griffinross2/Topiary-TrimBot/software/images/left_0.jpg

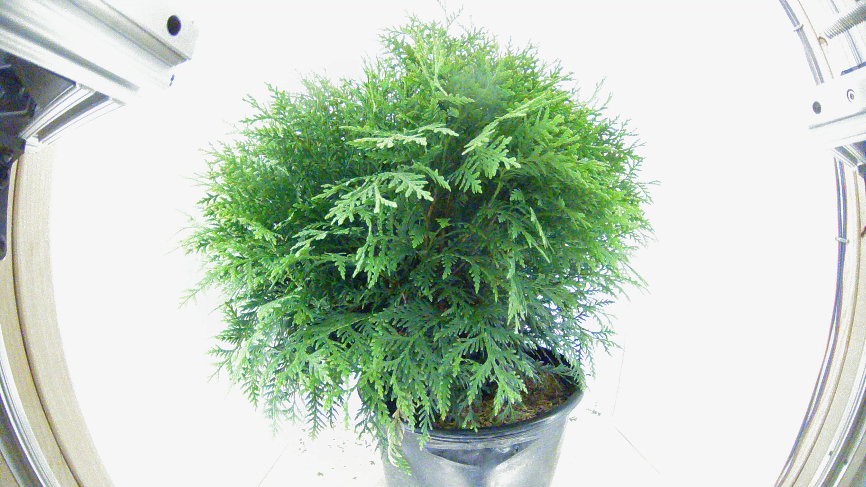
software/images/left_0.jpg
