griffinross2/Topiary-TrimBot/software/images/left_30.jpg

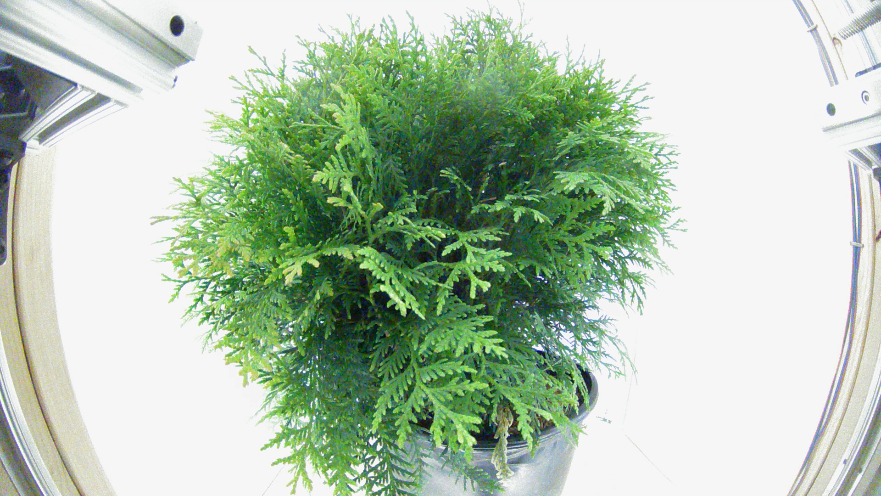
software/images/left_30.jpg
