griffinross2/Topiary-TrimBot/software/images/left_60.jpg

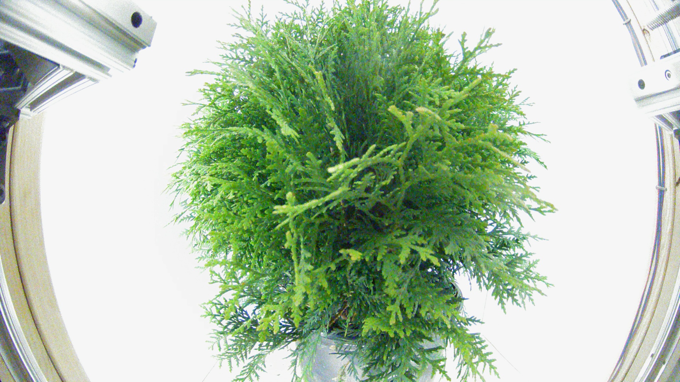
software/images/left_60.jpg
