griffinross2/Topiary-TrimBot/software/images/left_90.jpg

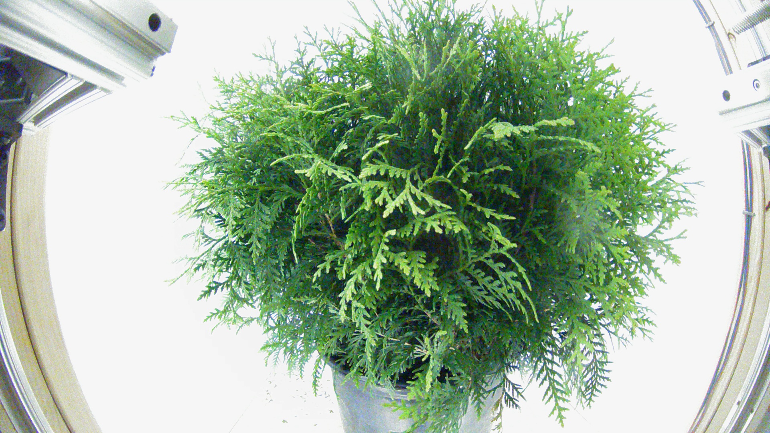
software/images/left_90.jpg
