griffinross2/Topiary-TrimBot/software/images/left_120.jpg

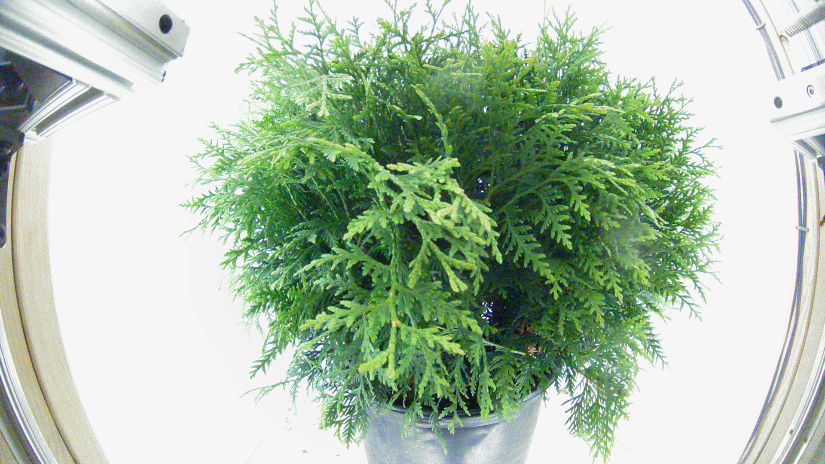
software/images/left_120.jpg
