griffinross2/Topiary-TrimBot/software/images/left_150.jpg

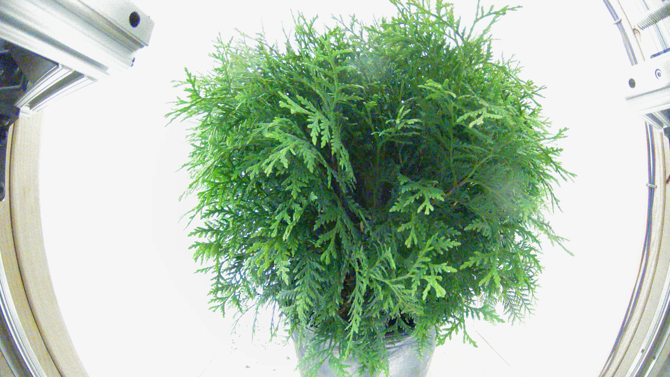
software/images/left_150.jpg
