griffinross2/Topiary-TrimBot/software/images/left_210.jpg

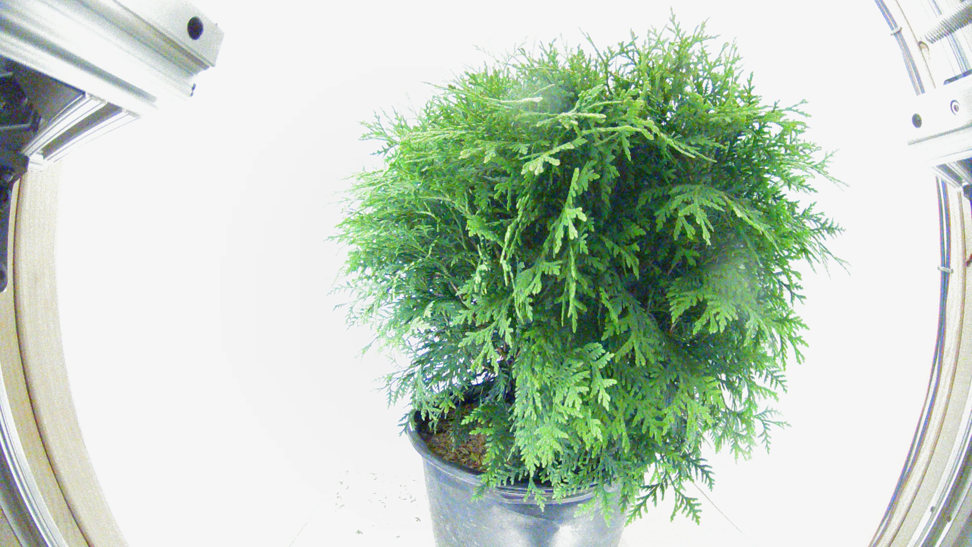
software/images/left_210.jpg
