griffinross2/Topiary-TrimBot/software/images/left_240.jpg

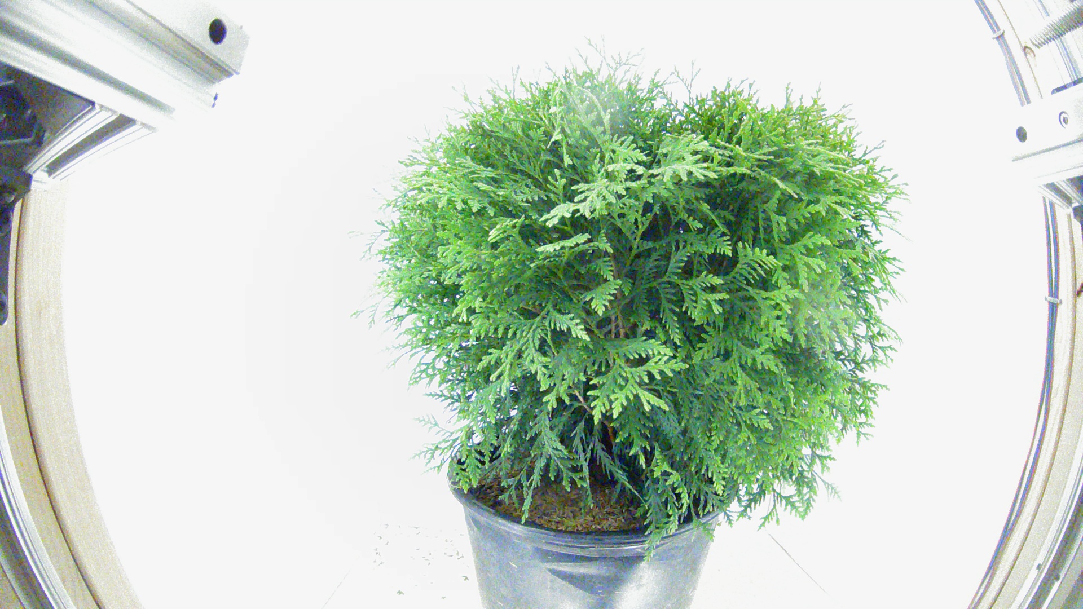
software/images/left_240.jpg
