griffinross2/Topiary-TrimBot/software/images/left_270.jpg

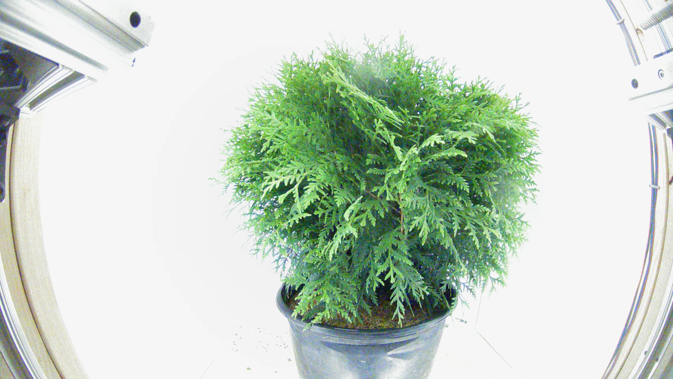
software/images/left_270.jpg
