griffinross2/Topiary-TrimBot/software/images/left_330.jpg

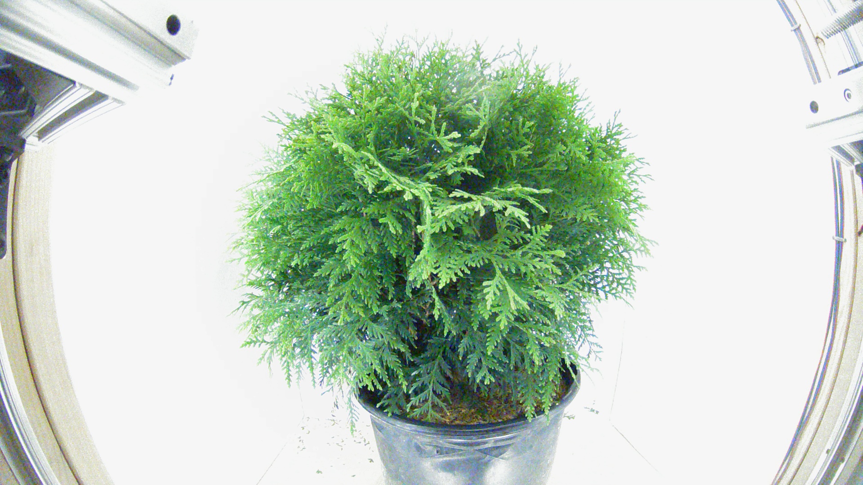
software/images/left_330.jpg
