griffinross2/Topiary-TrimBot/software/images/right_0.jpg

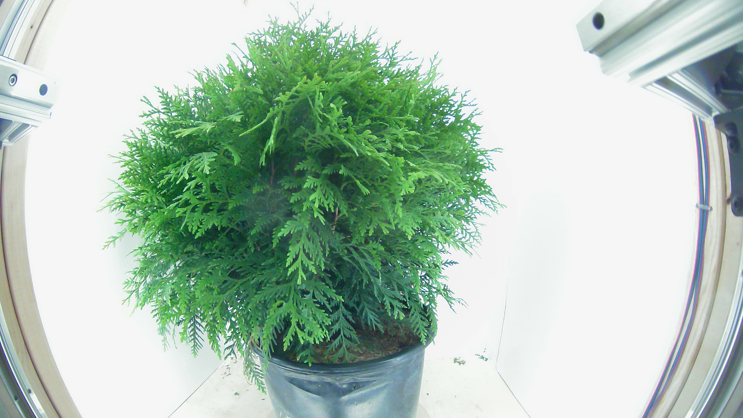
software/images/right_0.jpg
