griffinross2/Topiary-TrimBot/software/images/right_30.jpg

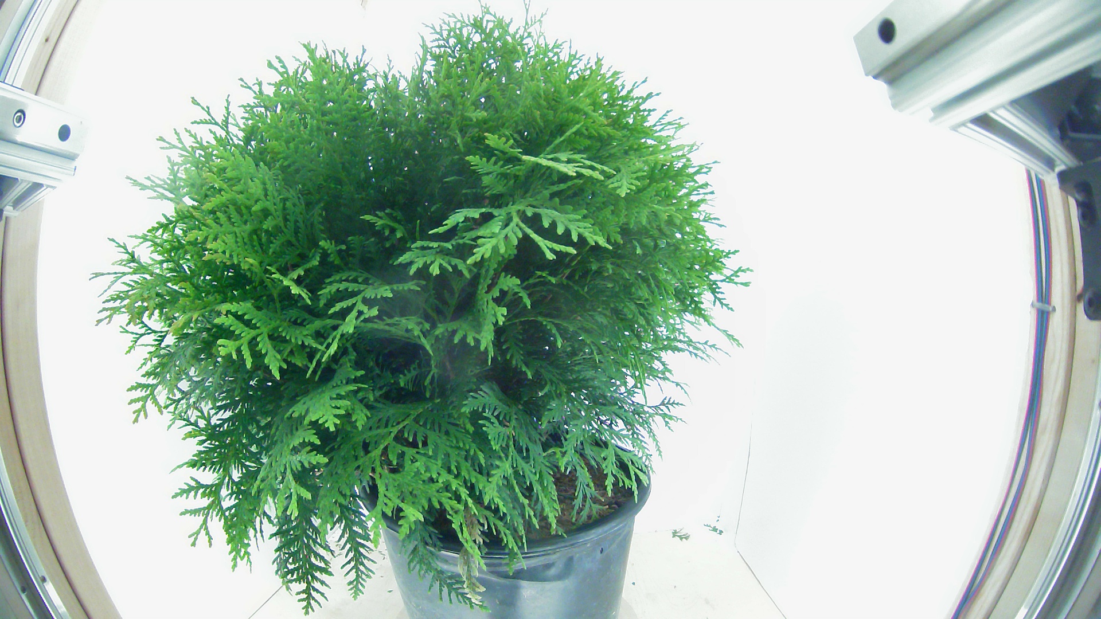
software/images/right_30.jpg
