griffinross2/Topiary-TrimBot/software/images/right_60.jpg

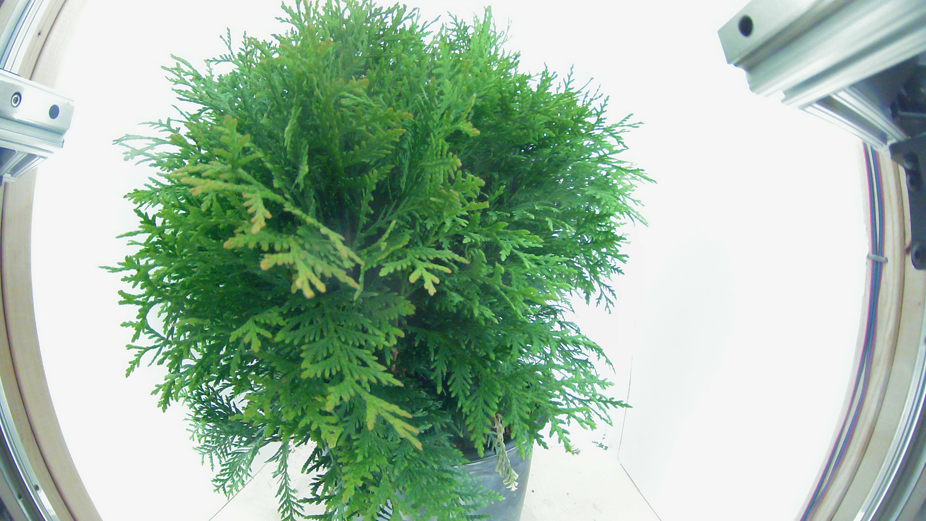
software/images/right_60.jpg
