griffinross2/Topiary-TrimBot/software/images/right_90.jpg

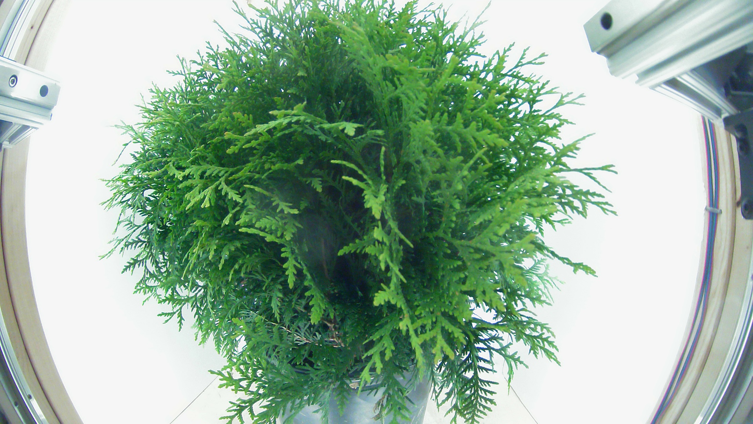
software/images/right_90.jpg
