griffinross2/Topiary-TrimBot/software/images/right_120.jpg

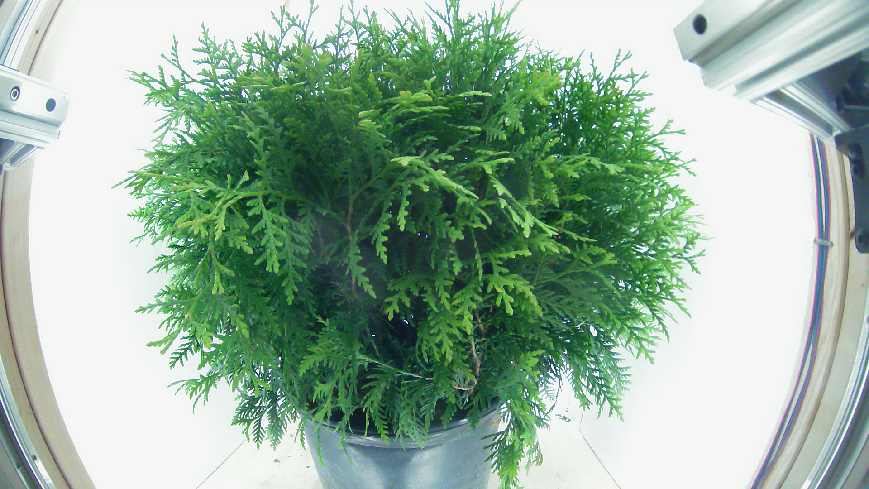
software/images/right_120.jpg
