griffinross2/Topiary-TrimBot/software/images/right_180.jpg

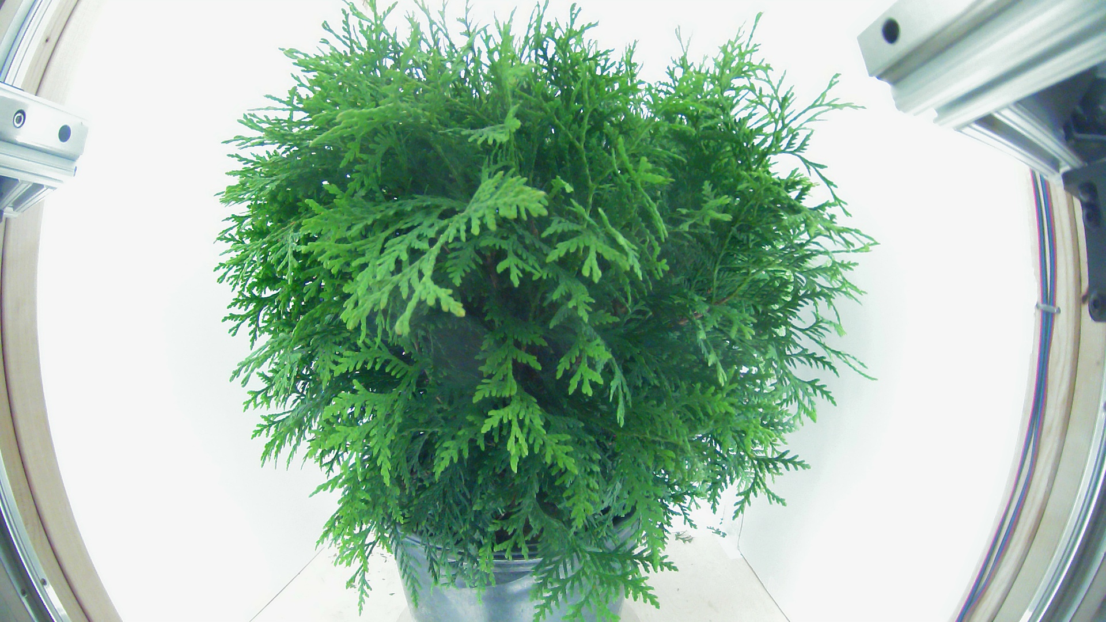
software/images/right_180.jpg
