griffinross2/Topiary-TrimBot/software/images/right_270.jpg

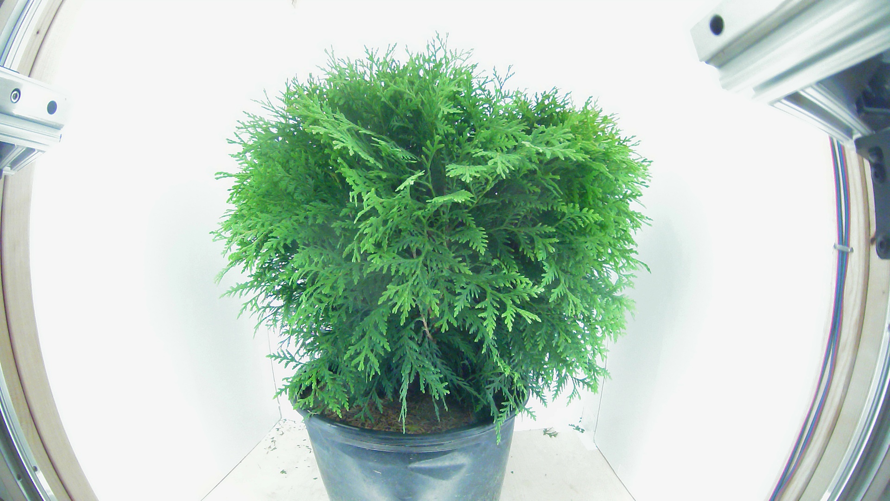
software/images/right_270.jpg
