griffinross2/Topiary-TrimBot/software/images/right_330.jpg

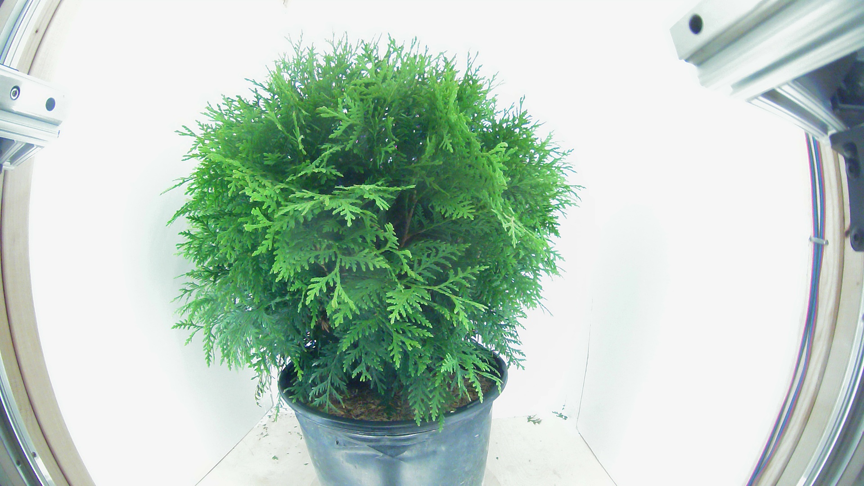
software/images/right_330.jpg
