griffinross2/Topiary-TrimBot/software/vision/checkerboards/WIN_20260413_22_22_19_Pro.jpg

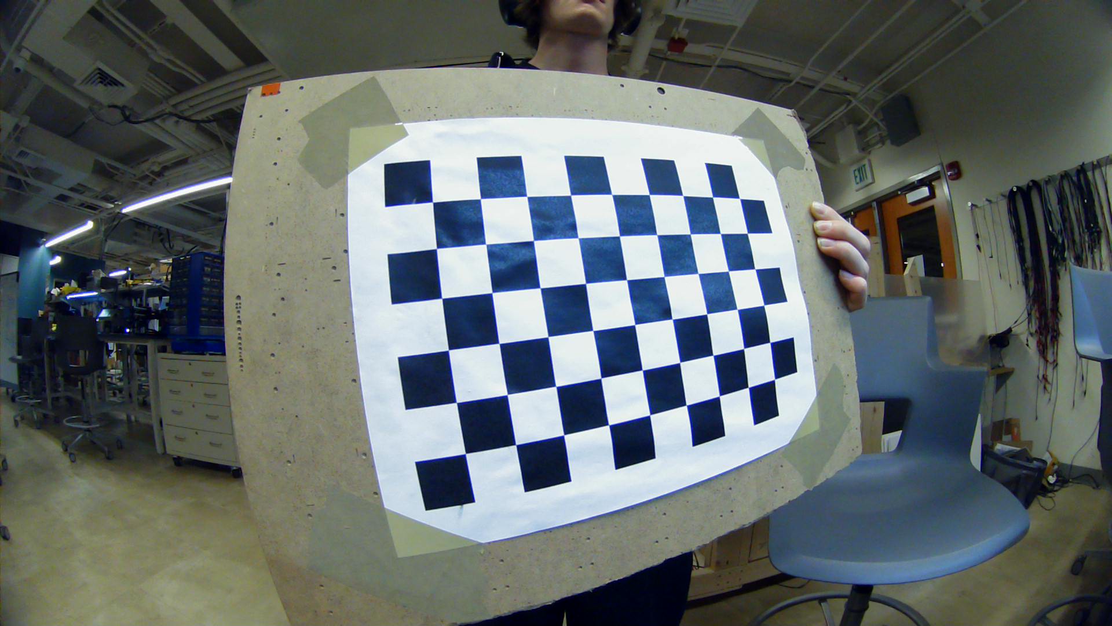
software/vision/checkerboards/WIN_20260413_22_22_19_Pro.jpg
