griffinross2/Topiary-TrimBot/software/vision/checkerboards/WIN_20260413_22_38_03_Pro.jpg

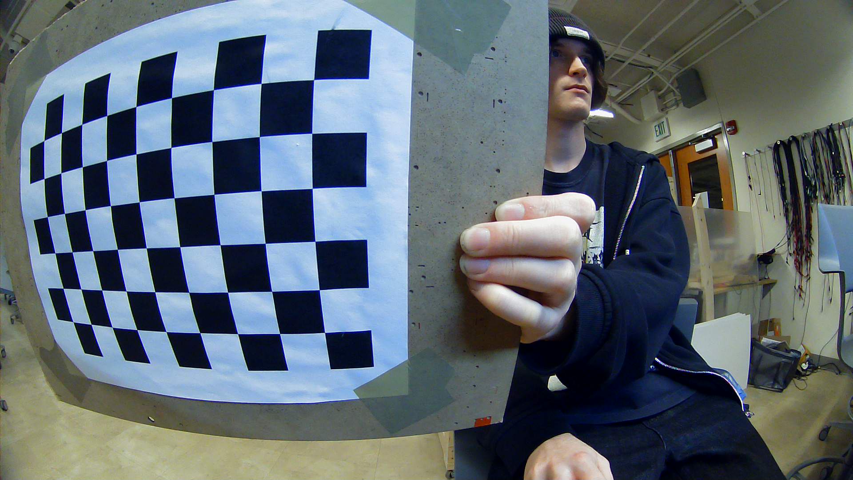
software/vision/checkerboards/WIN_20260413_22_38_03_Pro.jpg
