griffinross2/Topiary-TrimBot/software/vision/checkerboards/WIN_20260414_17_03_58_Pro.jpg

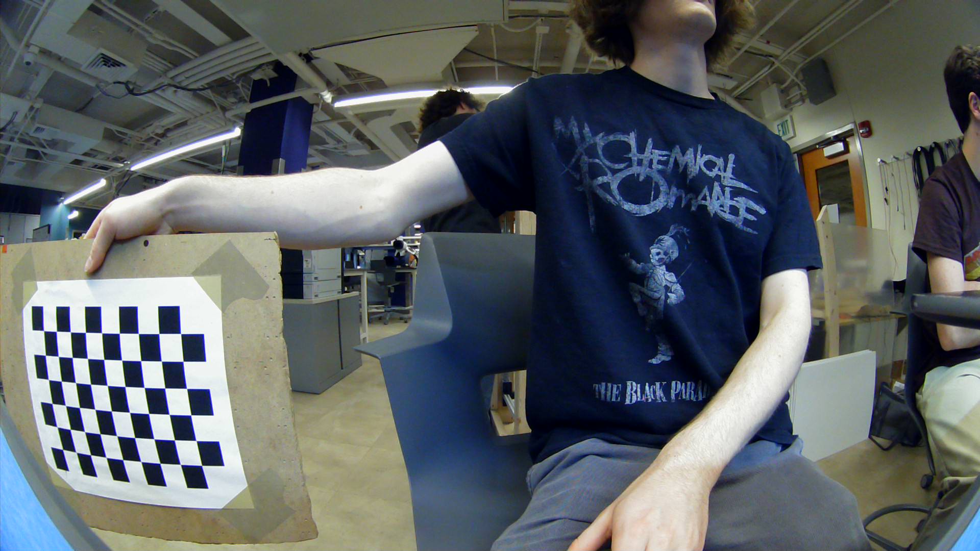
software/vision/checkerboards/WIN_20260414_17_03_58_Pro.jpg
