griffinross2/Topiary-TrimBot/experimental/cpp/plant_detect/images/pi/cal_5.jpg

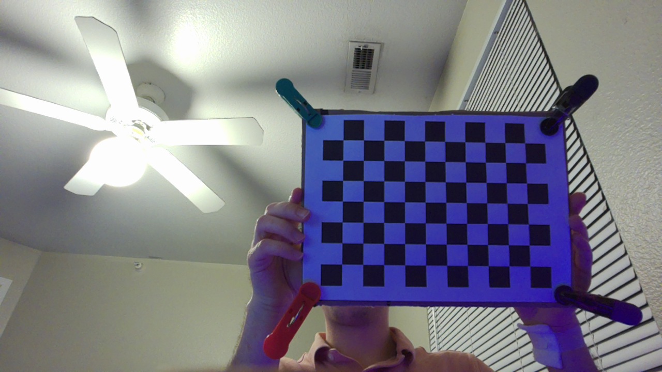
experimental/cpp/plant_detect/images/pi/cal_5.jpg
