griffinross2/Topiary-TrimBot/experimental/cpp/plant_detect/images/pi/cal_6.jpg

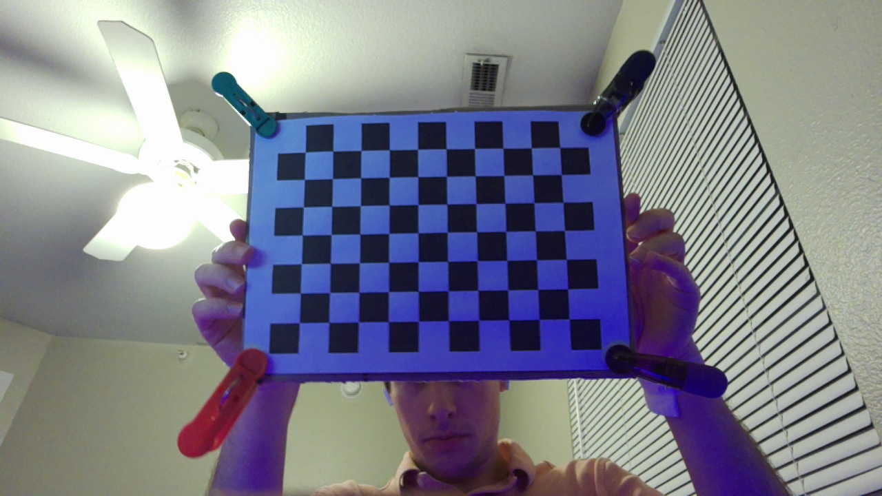
experimental/cpp/plant_detect/images/pi/cal_6.jpg
