griffinross2/Topiary-TrimBot/experimental/cpp/plant_detect/images/WIN_20251111_21_14_15_Pro.jpg

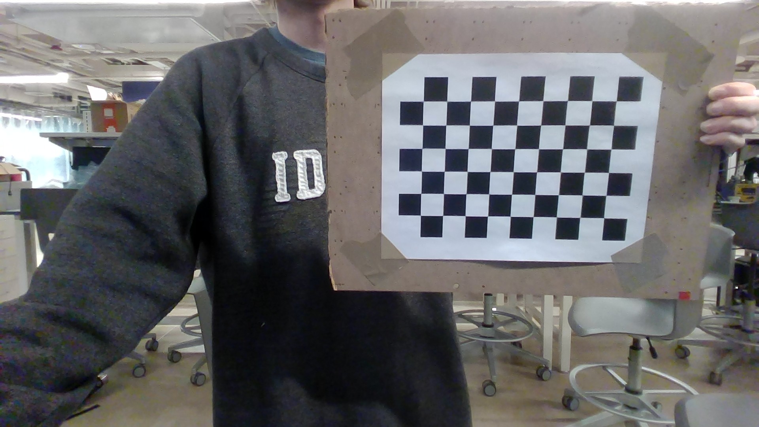
experimental/cpp/plant_detect/images/WIN_20251111_21_14_15_Pro.jpg
