griffinross2/Topiary-TrimBot/experimental/cpp/plant_detect/images/WIN_20251111_21_15_57_Pro.jpg

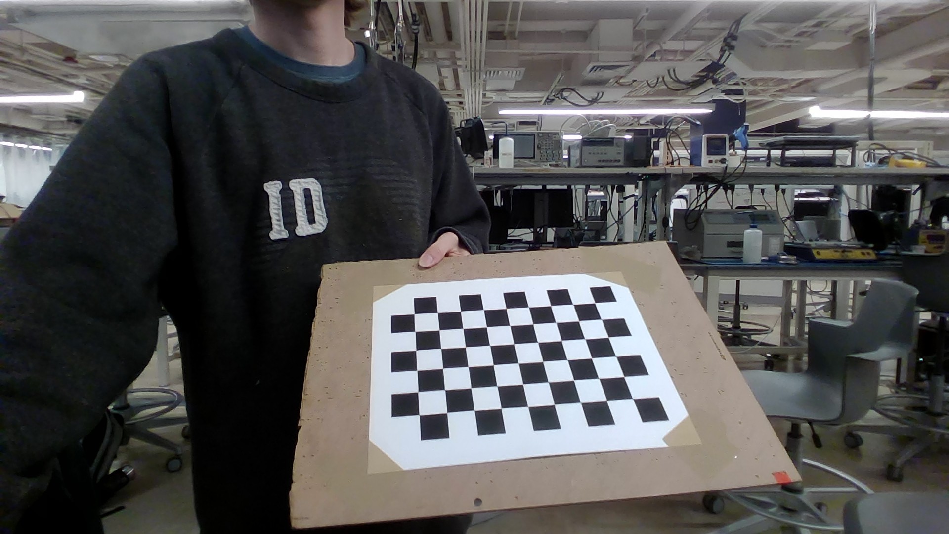
experimental/cpp/plant_detect/images/WIN_20251111_21_15_57_Pro.jpg
