griffinross2/Topiary-TrimBot/experimental/python-notebooks/plant_detect/image324x324outside.jpg

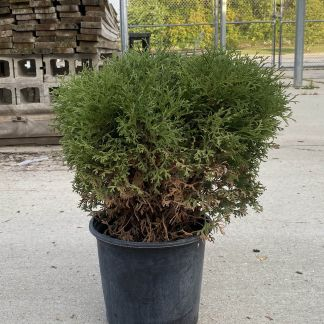
experimental/python-notebooks/plant_detect/image324x324outside.jpg
