griffinross2/Topiary-TrimBot/experimental/python-notebooks/plant_detect/left_rot_1.jpg

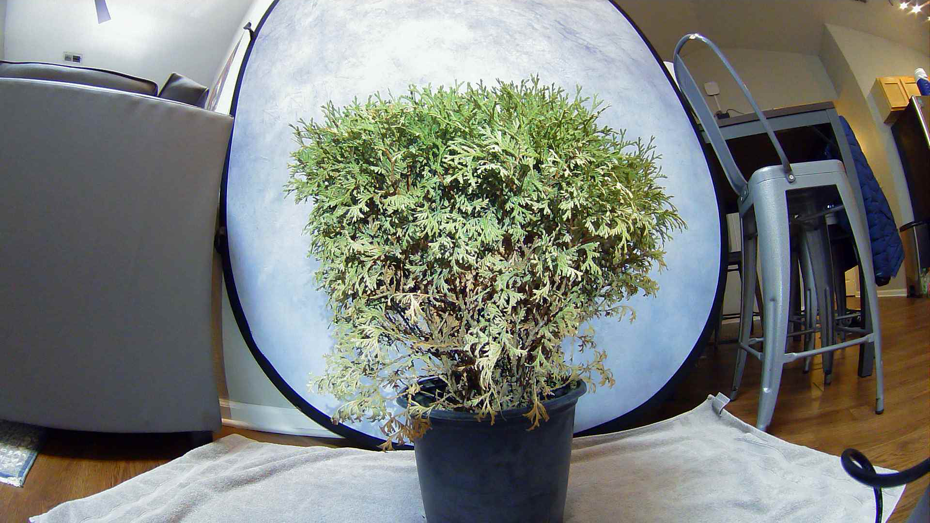
experimental/python-notebooks/plant_detect/left_rot_1.jpg
