griffinross2/Topiary-TrimBot/software/calibration_images/left/0.jpg

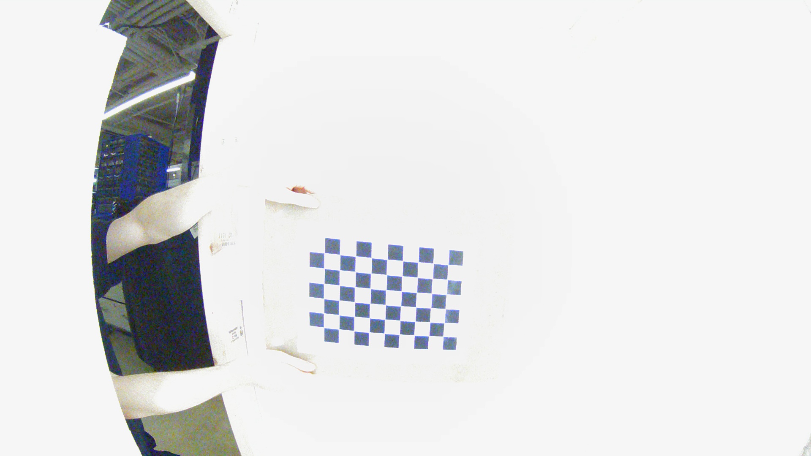
software/calibration_images/left/0.jpg
