griffinross2/Topiary-TrimBot/software/calibration_images/left/1.jpg

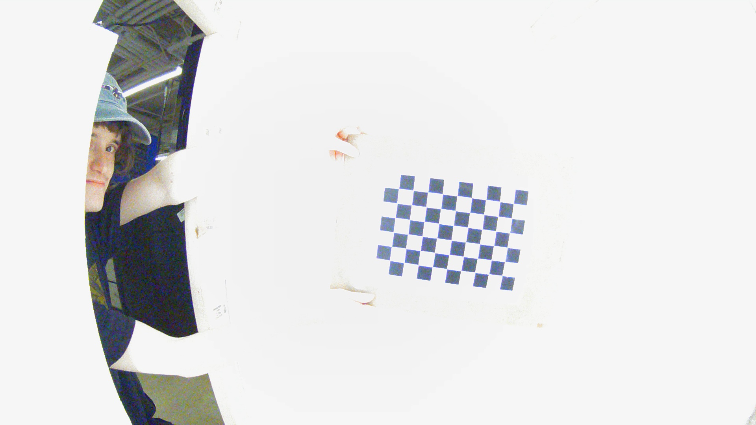
software/calibration_images/left/1.jpg
