griffinross2/Topiary-TrimBot/software/calibration_images/left/2.jpg

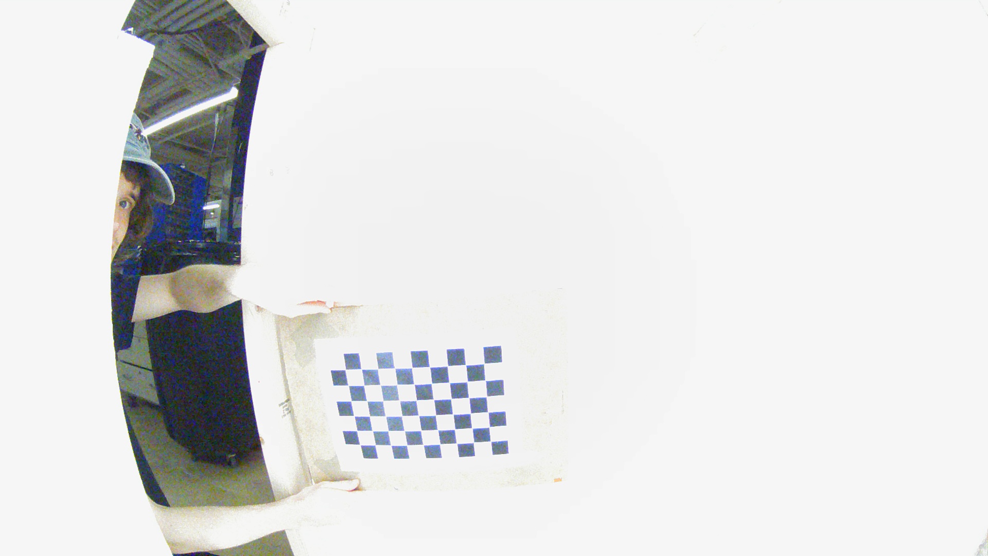
software/calibration_images/left/2.jpg
