griffinross2/Topiary-TrimBot/software/calibration_images/left/3.jpg

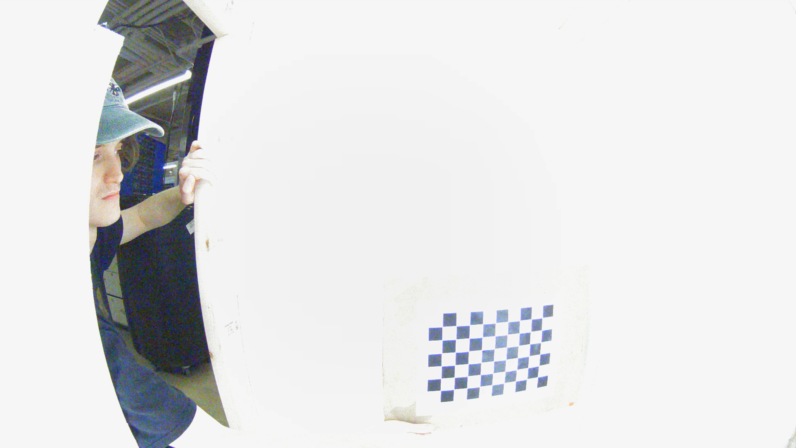
software/calibration_images/left/3.jpg
