griffinross2/Topiary-TrimBot/software/calibration_images/left/5.jpg

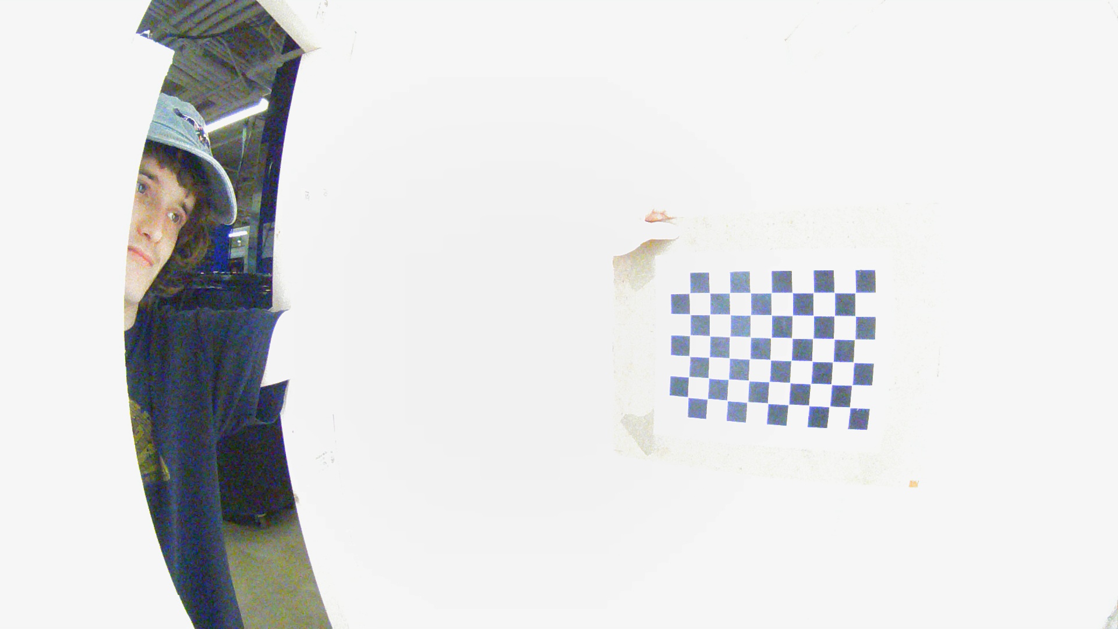
software/calibration_images/left/5.jpg
