griffinross2/Topiary-TrimBot/software/calibration_images/left/6.jpg

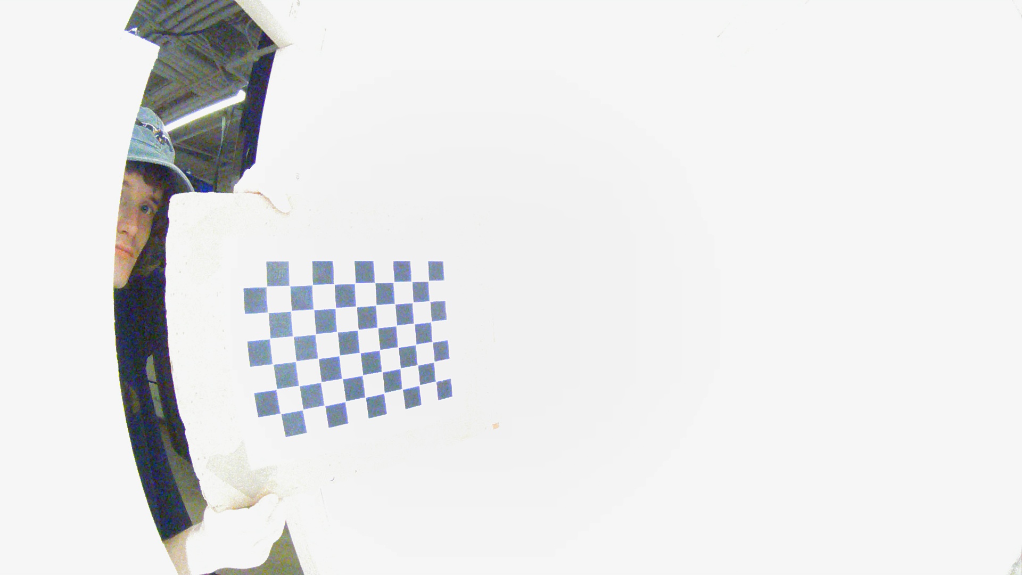
software/calibration_images/left/6.jpg
