griffinross2/Topiary-TrimBot/software/calibration_images/left/8.jpg

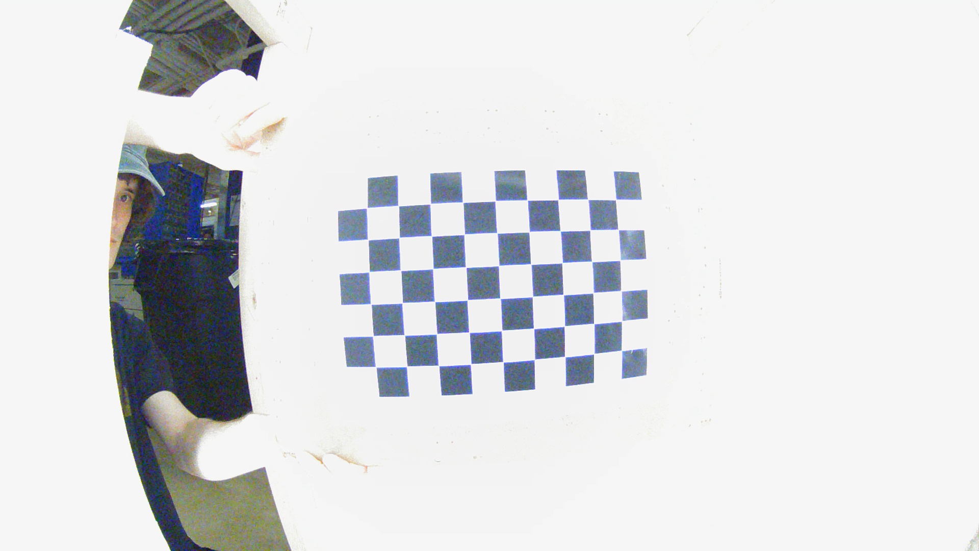
software/calibration_images/left/8.jpg
