griffinross2/Topiary-TrimBot/software/calibration_images/left/10.jpg

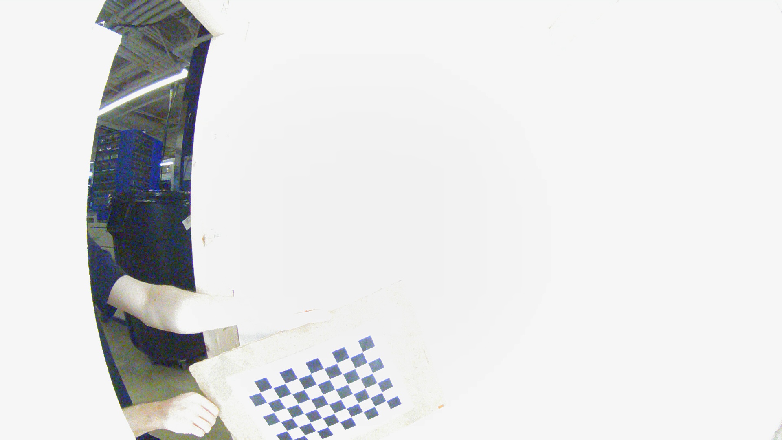
software/calibration_images/left/10.jpg
