griffinross2/Topiary-TrimBot/software/calibration_images/left/13.jpg

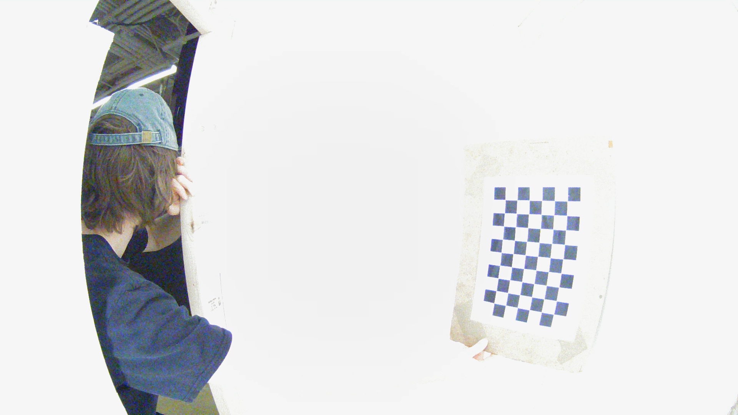
software/calibration_images/left/13.jpg
