griffinross2/Topiary-TrimBot/software/calibration_images/left/14.jpg

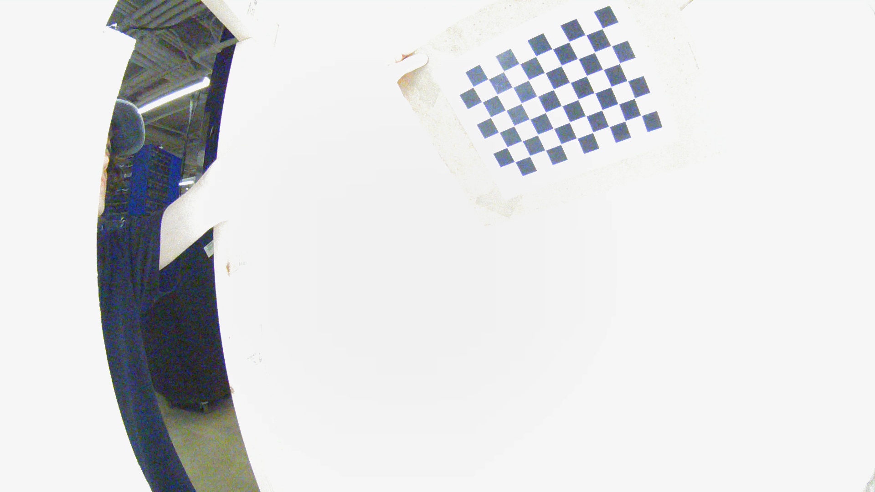
software/calibration_images/left/14.jpg
