griffinross2/Topiary-TrimBot/software/calibration_images/left/15.jpg

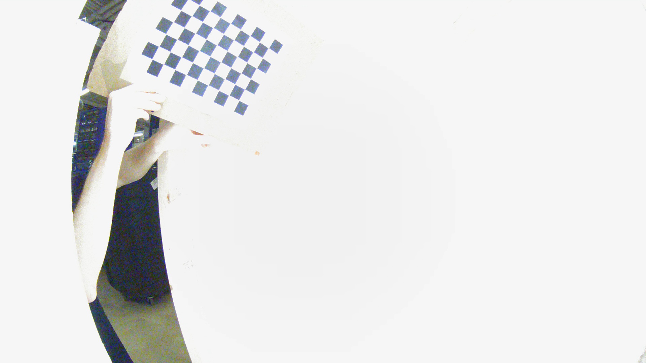
software/calibration_images/left/15.jpg
