griffinross2/Topiary-TrimBot/software/calibration_images/left/16.jpg

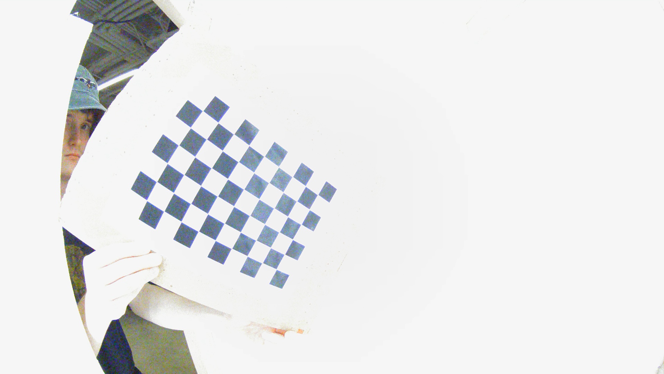
software/calibration_images/left/16.jpg
