griffinross2/Topiary-TrimBot/software/calibration_images/left/18.jpg

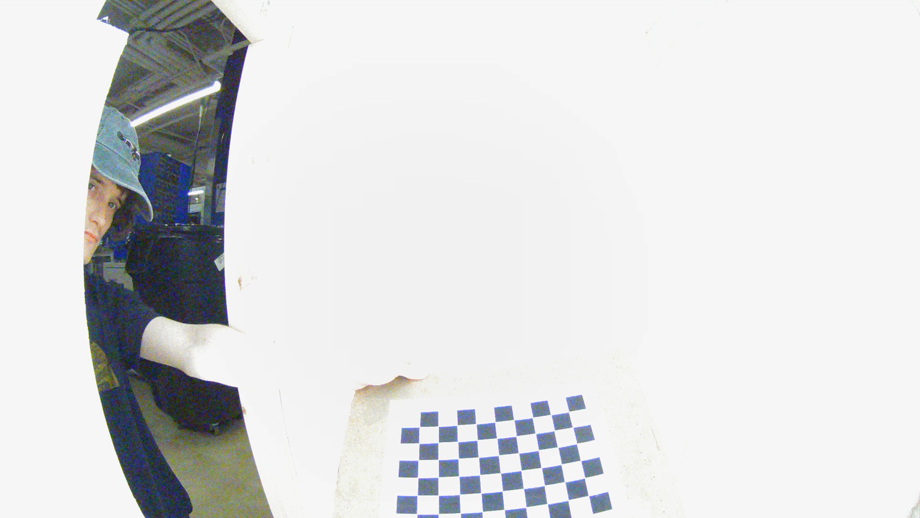
software/calibration_images/left/18.jpg
