griffinross2/Topiary-TrimBot/software/calibration_images/left/19.jpg

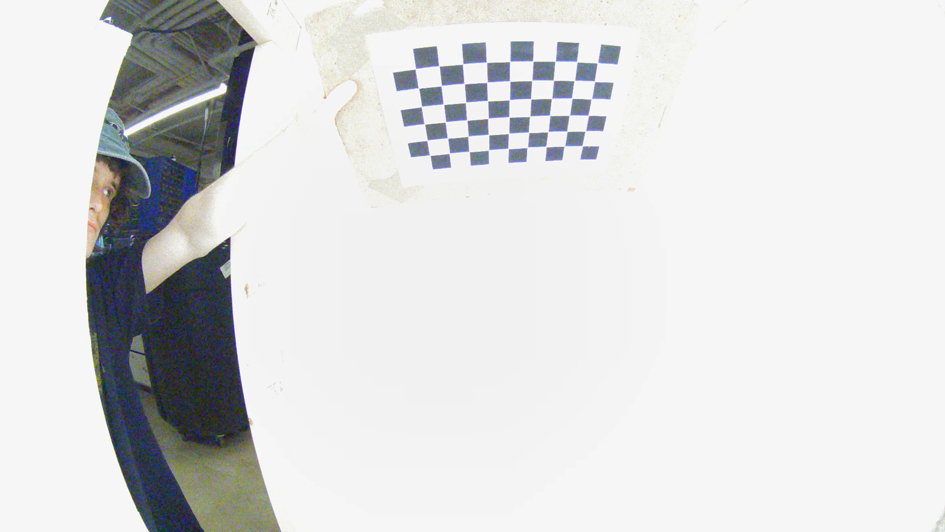
software/calibration_images/left/19.jpg
