griffinross2/Topiary-TrimBot/software/calibration_images/right/1.jpg

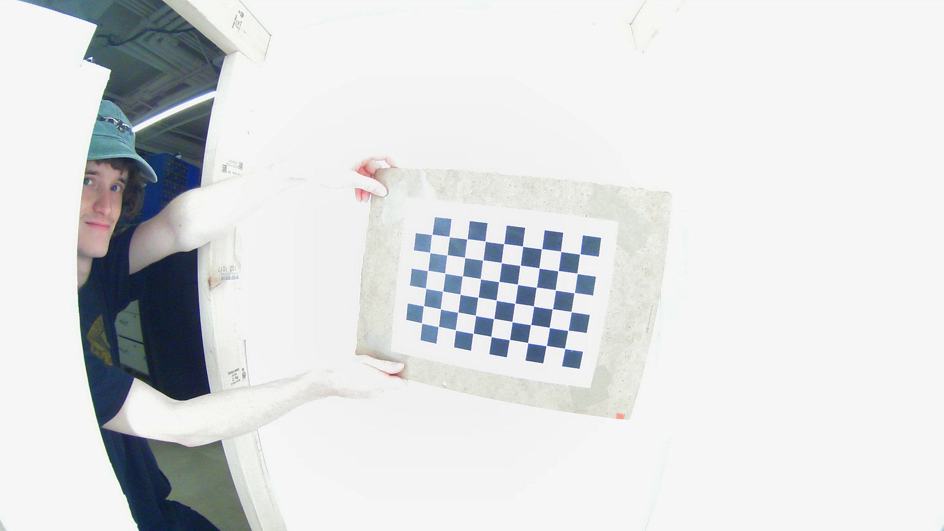
software/calibration_images/right/1.jpg
