griffinross2/Topiary-TrimBot/software/calibration_images/right/2.jpg

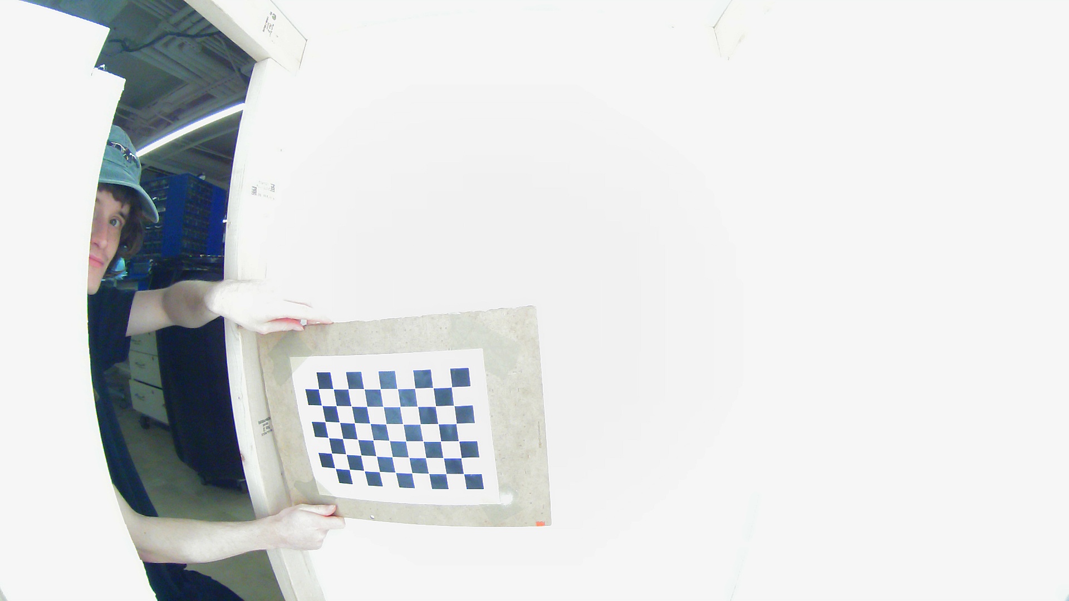
software/calibration_images/right/2.jpg
