griffinross2/Topiary-TrimBot/software/calibration_images/right/3.jpg

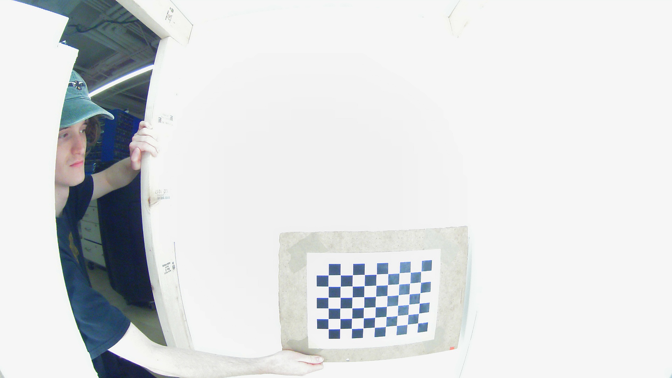
software/calibration_images/right/3.jpg
