griffinross2/Topiary-TrimBot/software/calibration_images/right/5.jpg

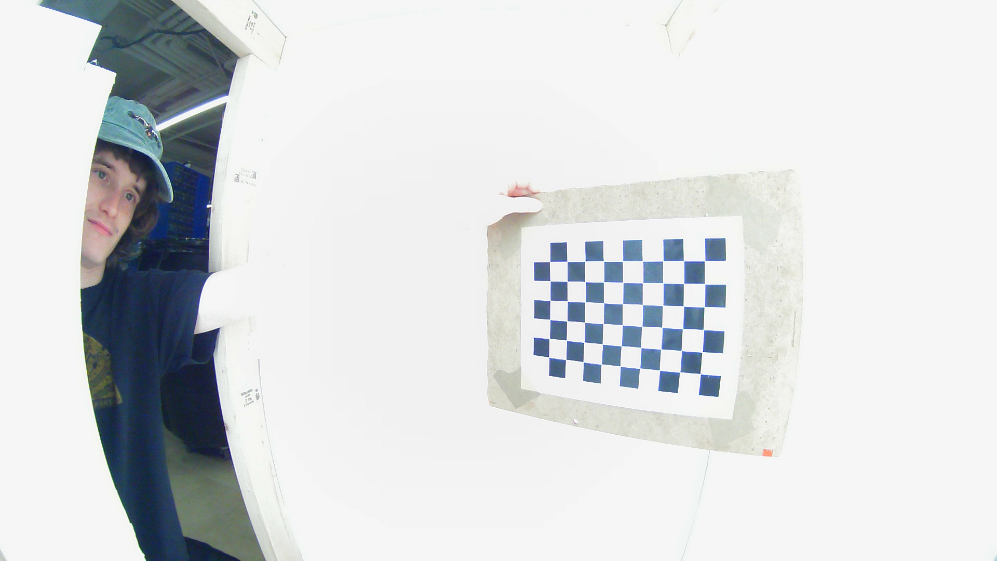
software/calibration_images/right/5.jpg
