griffinross2/Topiary-TrimBot/software/calibration_images/right/6.jpg

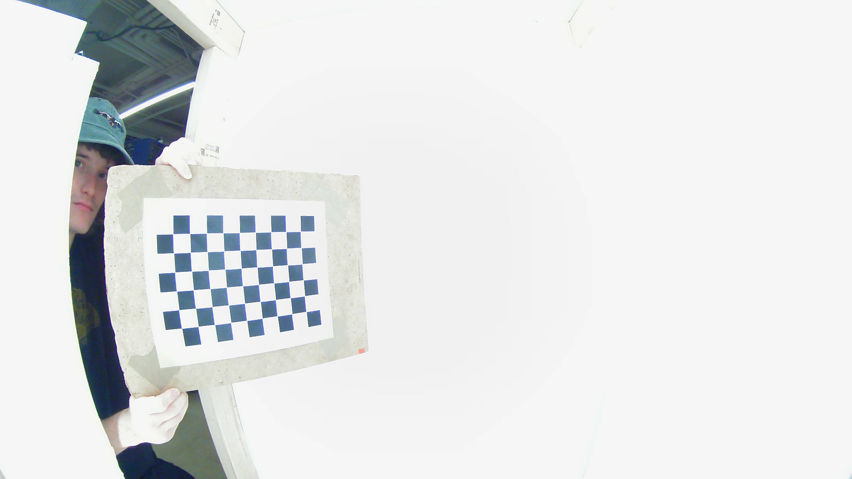
software/calibration_images/right/6.jpg
