griffinross2/Topiary-TrimBot/software/calibration_images/right/7.jpg

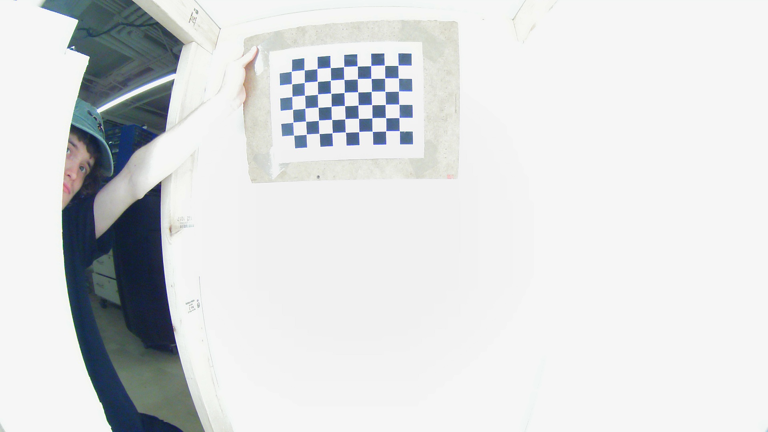
software/calibration_images/right/7.jpg
