griffinross2/Topiary-TrimBot/software/calibration_images/right/10.jpg

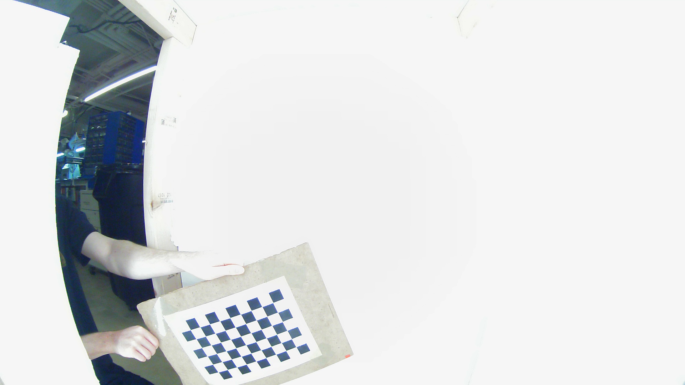
software/calibration_images/right/10.jpg
