griffinross2/Topiary-TrimBot/software/calibration_images/right/11.jpg

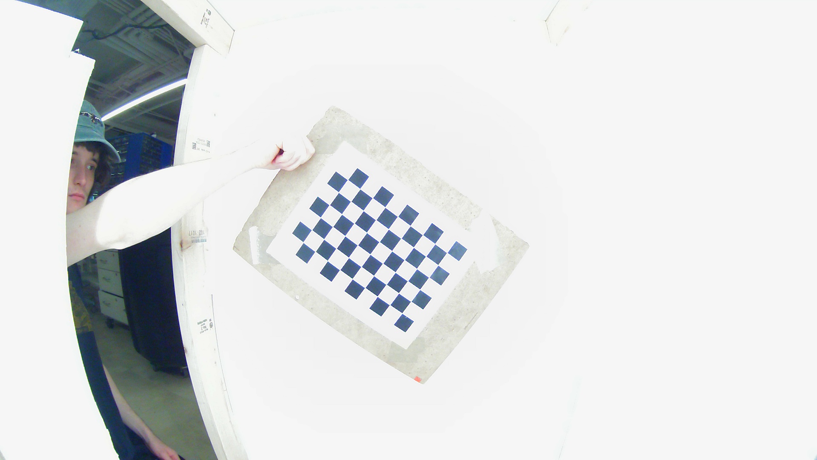
software/calibration_images/right/11.jpg
