griffinross2/Topiary-TrimBot/software/calibration_images/right/13.jpg

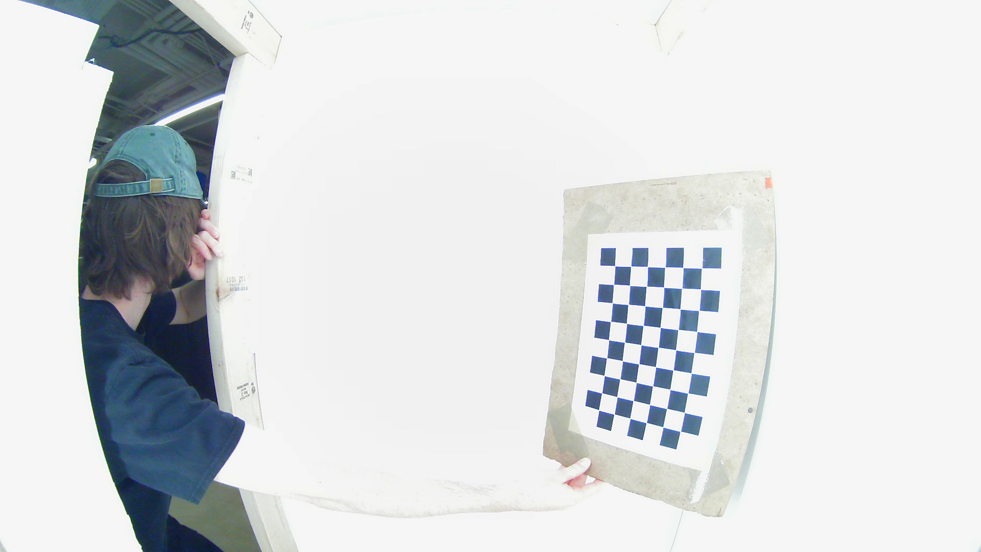
software/calibration_images/right/13.jpg
