griffinross2/Topiary-TrimBot/software/calibration_images/right/14.jpg

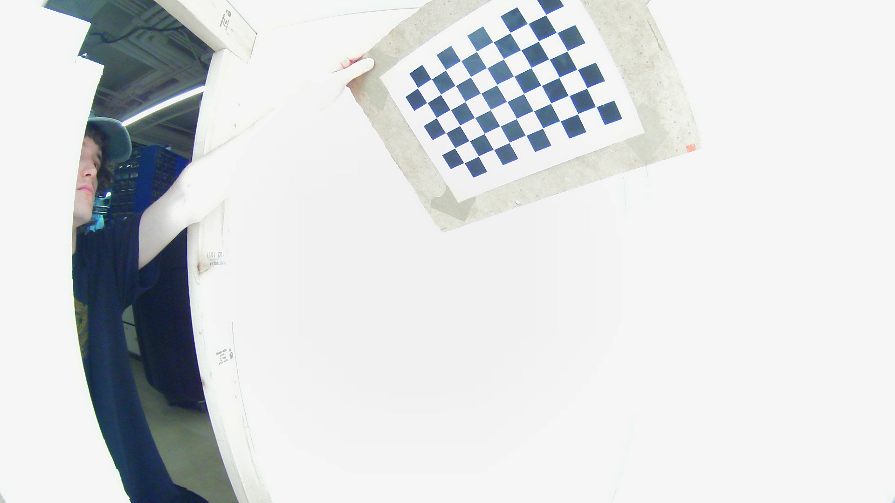
software/calibration_images/right/14.jpg
