griffinross2/Topiary-TrimBot/software/calibration_images/right/15.jpg

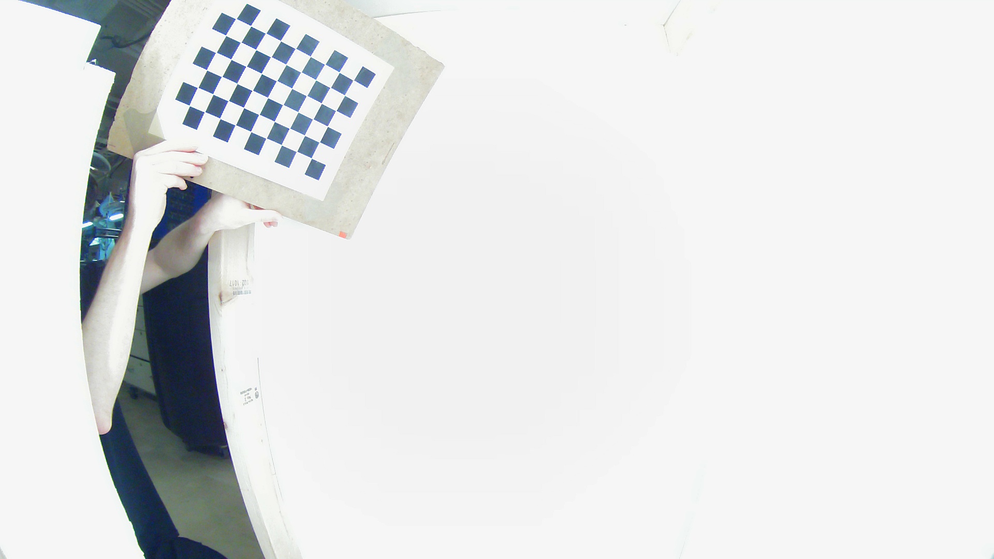
software/calibration_images/right/15.jpg
