griffinross2/Topiary-TrimBot/software/calibration_images/right/16.jpg

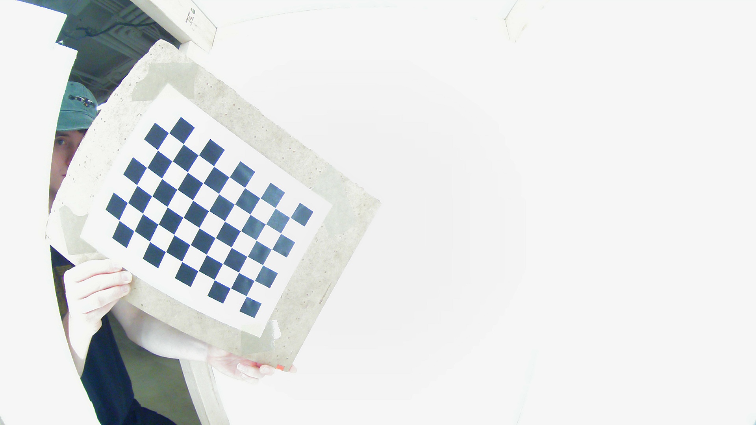
software/calibration_images/right/16.jpg
