griffinross2/Topiary-TrimBot/software/calibration_images/right/17.jpg

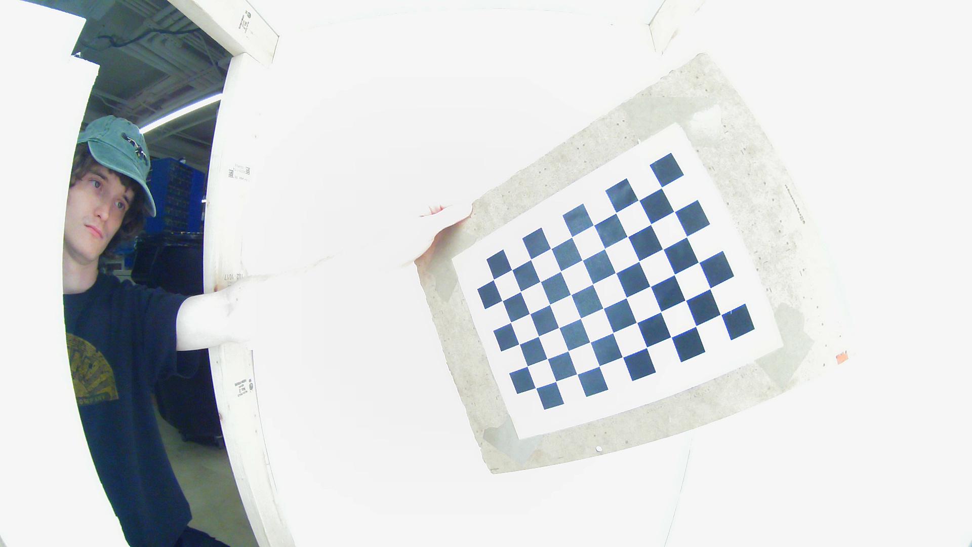
software/calibration_images/right/17.jpg
