griffinross2/Topiary-TrimBot/software/calibration_images/right/18.jpg

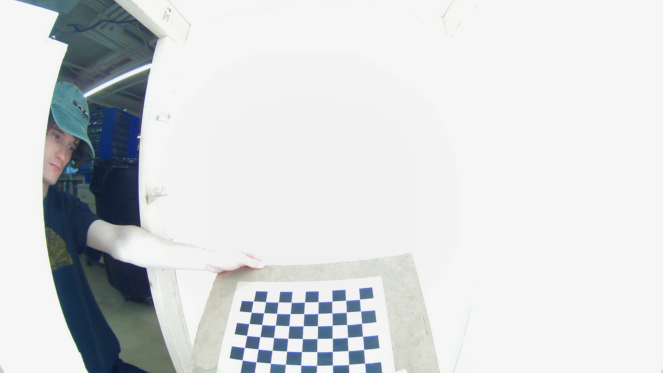
software/calibration_images/right/18.jpg
