griffinross2/Topiary-TrimBot/software/crc16.py

# crc16.py based on:
# Github Gist by rafacouto : https://gist.github.com/rafacouto/59326c90d6a55f86a3ba

ccitt_hash = [
    0x0000,
    0x1021,
    0x2042,
    0x3063,
    0x4084,
    0x50a5,
    0x60c6,
    0x70e7,
    0x8108,
    0x9129,
    0xa14a,
    0xb16b,
    0xc18c,
    0xd1ad,
    0xe1ce,
    0xf1ef,
    0x1231,
    0x0210,
    0x3273,
    0x2252,
    0x52b5,
    0x4294,
    0x72f7,
    0x62d6,
    0x9339,
    0x8318,
    0xb37b,
    0xa35a,
    0xd3bd,
    0xc39c,
    0xf3ff,
    0xe3de,
    0x2462,
    0x3443,
    0x0420,
    0x1401,
    0x64e6,
    0x74c7,
    0x44a4,
    0x5485,
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
]

def crc16_ccitt(buffer: bytes):
    idx = 0
    size = len(buffer)

    crc = 0
    while size > 0:
        size -= 1
        crc = (crc << 8) ^ ccitt_hash[((crc >> 8) ^ buffer[idx]) & 0x00FF]
        idx += 1

    return crc & 0xFFFF
