griffinross2/Topiary-TrimBot/experimental/lcd_prototyping/Core/Src/main.c

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
/* Includes ------------------------------------------------------------------*/
#include "main.h"

/* USER CODE BEGIN Includes */
#include <stdio.h>
#include "lcd.h"
/* USER CODE END Includes */

DSI_HandleTypeDef hdsi;

I2C_HandleTypeDef hi2c1;

LTDC_HandleTypeDef hltdc;

TIM_HandleTypeDef htim3;

UART_HandleTypeDef huart6;

SDRAM_HandleTypeDef hsdram1;

void SystemClock_Config(void);
static void MX_GPIO_Init(void);
static void MX_USART6_UART_Init(void);
static void MX_LTDC_Init(void);
static void MX_DSIHOST_DSI_Init(void);
static void MX_FMC_Init(void);
static void MX_I2C1_Init(void);
static void MX_TIM3_Init(void);
/* USER CODE BEGIN 0 */
int __io_putchar(int ch) {
	HAL_UART_Transmit(&huart6, (uint8_t*)&ch, 1, 50);
	return ch;
}
/* USER CODE END 0 */

/**
  * @brief  The application entry point.
  * @retval int
  */
int main(void)
{

  /* MCU Configuration--------------------------------------------------------*/

  /* Reset of all peripherals, Initializes the Flash interface and the Systick. */
  HAL_Init();

  /* Configure the system clock */
  SystemClock_Config();

  /* Initialize all configured peripherals */
  MX_GPIO_Init();
  MX_USART6_UART_Init();
  MX_LTDC_Init();
  MX_DSIHOST_DSI_Init();
  MX_FMC_Init();
  MX_I2C1_Init();
  MX_TIM3_Init();
  /* USER CODE BEGIN 2 */
  if (lcd_init() != LCD_OK) {
	  printf("LCD failed to initialize!\n");
	  return 1;
  }
  printf("LCD init success\n");
  /* USER CODE END 2 */

  /* Infinite loop */
  /* USER CODE BEGIN WHILE */
  while (1)
  {
    /* USER CODE END WHILE */

    /* USER CODE BEGIN 3 */
	  printf("cuh\n");
	  HAL_Delay(1000);
  }

  return 0;
  /* USER CODE END 3 */
}

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
