griffinross2/Topiary-TrimBot/experimental/lcd_prototyping_platformio/src/lcd.cpp

/*
 * lcd.c
 *
 *  Created on: Nov 11, 2025
 *      Author: griff
 */

#include "lcd.h"

#include <stdio.h>
#include <string.h>
#include <algorithm>

#include "ltdc_dsi.h"
#include "nt35510.h"
#include "ft6336g.h"
#include "profiler.h"

#define LCD_RESET_PORT GPIOH
#define LCD_RESET_PIN GPIO_PIN_7

DSI_HandleTypeDef* hdsi;
LTDC_HandleTypeDef* hltdc;
DMA2D_HandleTypeDef hdma2d;

// Double-buffered setup
static ColorRGB565 __attribute__((
    section(".ext_ram"))) s_foreground_buffer_0[LCD_WIDTH * LCD_HEIGHT];
static ColorRGB565 __attribute__((
    section(".ext_ram"))) s_foreground_buffer_1[LCD_WIDTH * LCD_HEIGHT];

static ColorRGB565** s_foreground_buffers = (ColorRGB565*[]){
    s_foreground_buffer_0,
    s_foreground_buffer_1,
};
static volatile int s_current_frontbuffer = 0;

// Sorry about macros
#define FRONTBUFFER s_foreground_buffers[s_current_frontbuffer]
#define BACKBUFFER s_foreground_buffers[1 - s_current_frontbuffer]

// EOF callback
void lcd_end_of_refresh_callback(DSI_HandleTypeDef* hdsi);

// Refresh request flag
static volatile bool s_refreshing = false;

#define DMA_MAX_TRANSFER_SIZE 65535UL

ColorRGB565 rgb888_to_rgb565(ColorRGB888 color) {
    return ((color >> 8) & 0xF800) | ((color >> 5) & 0x07E0) |
           ((color >> 3) & 0x001F);
}

ColorRGB888 rgb565_to_rgb888(ColorRGB565 color) {
    return (color & 0xF800) << 8 | (color & 0x07E0) << 5 |
           (color & 0x001F) << 3;
}

Status lcd_init() {
    ltdc_dsi_init();
    hltdc = ltdc_get_handle();
    hdsi = dsi_get_handle();

    GPIO_InitTypeDef lcd_reset = {
        .Pin = LCD_RESET_PIN,
        .Mode = GPIO_MODE_OUTPUT_PP,
        .Pull = GPIO_NOPULL,
        .Speed = GPIO_SPEED_FREQ_LOW,
        .Alternate = 0,
    };

    // Reset the LCD and touchscreen
    HAL_GPIO_Init(LCD_RESET_PORT, &lcd_reset);
    HAL_GPIO_WritePin(LCD_RESET_PORT, LCD_RESET_PIN, GPIO_PIN_SET);
    HAL_Delay(10);
    HAL_GPIO_WritePin(LCD_RESET_PORT, LCD_RESET_PIN, GPIO_PIN_RESET);
    HAL_Delay(20);
    HAL_GPIO_WritePin(LCD_RESET_PORT, LCD_RESET_PIN, GPIO_PIN_SET);
    HAL_Delay(20);

    __HAL_RCC_DMA2D_CLK_ENABLE();
    memset(&hdma2d, 0, sizeof(hdma2d));
    hdma2d.Instance = DMA2D;
    hdma2d.Init.Mode = DMA2D_R2M;
    hdma2d.Init.ColorMode = DMA2D_RGB565;
    hdma2d.Init.OutputOffset = 0;
    hdma2d.XferCpltCallback = nullptr;
    hdma2d.XferErrorCallback = nullptr;
    hdma2d.LayerCfg[0].InputOffset = 0;
    hdma2d.LayerCfg[0].InputColorMode = DMA2D_RGB565;
    hdma2d.LayerCfg[0].AlphaMode = DMA2D_NO_MODIF_ALPHA;
    hdma2d.LayerCfg[0].InputAlpha = 0xFF;
    hdma2d.LayerCfg[1].InputOffset = 0;
    hdma2d.LayerCfg[1].InputColorMode = DMA2D_RGB565;
    hdma2d.LayerCfg[1].AlphaMode = DMA2D_NO_MODIF_ALPHA;
    hdma2d.LayerCfg[1].InputAlpha = 0xFF;

    // Initialize the DMA2D
    if (HAL_DMA2D_Init(&hdma2d) != HAL_OK) {
        return STATUS_ERROR;
    }

    if (HAL_DMA2D_ConfigLayer(&hdma2d, 0) != HAL_OK) {
        return STATUS_ERROR;
    }

    if (HAL_DMA2D_ConfigLayer(&hdma2d, 1) != HAL_OK) {
        return STATUS_ERROR;
    }

    // LCD init
    if (nt35510_init(hdsi) != STATUS_OK) {
        return STATUS_ERROR;
    }
    nt35510_set_brightness(hdsi, 200);

    // Blank both buffers
    memset(s_foreground_buffer_0, 0xFF, sizeof(s_foreground_buffer_0));
    memset(s_foreground_buffer_1, 0xFF, sizeof(s_foreground_buffer_1));

    // Register refresh end callback
    HAL_DSI_RegisterCallback(hdsi, HAL_DSI_ENDOF_REFRESH_CB_ID,
                             lcd_end_of_refresh_callback);

    lcd_refresh();

    HAL_LTDC_SetAddress(hltdc, (uint32_t)FRONTBUFFER, LTDC_LAYER_2);

    // Touchscreen init
    // Give some time after reset for the TS driver to become ready
    HAL_Delay(300);

    if (ft6336g_init() != STATUS_OK) {
        return STATUS_ERROR;
    }

    return STATUS_OK;
}

void lcd_swap_buffers() {
    PROFILER_ENTER();

    // Wait til not refreshing
    while (s_refreshing) {
    }

    // Set this so we don't try to swap again while refreshing
    s_refreshing = true;

    // Swap the buffer index
    s_current_frontbuffer = 1 - s_current_frontbuffer;

    // Set the new front buffer and refresh
    lcd_set_foreground(FRONTBUFFER);

    PROFILER_EXIT();
}

ColorRGB565* lcd_get_backbuffer() {
    return BACKBUFFER;
}

ColorRGB565* lcd_get_frontbuffer() {
    return FRONTBUFFER;
}

void lcd_refresh() {
    HAL_DSI_Refresh(hdsi);
}

void lcd_set_foreground(const ColorRGB565* fb_address) {
    HAL_DSI_Stop(hdsi);
    __HAL_LTDC_LAYER_DISABLE(hltdc, LTDC_LAYER_2);
    HAL_LTDC_SetAddress(hltdc, (uint32_t)fb_address, LTDC_LAYER_2);
    __HAL_LTDC_LAYER_ENABLE(hltdc, LTDC_LAYER_2);
    HAL_DSI_Start(hdsi);
    lcd_refresh();
}

void lcd_set_background(const ColorRGB565* fb_address) {
    HAL_DSI_Stop(hdsi);
    __HAL_LTDC_LAYER_DISABLE(hltdc, LTDC_LAYER_1);
    HAL_LTDC_SetAddress(hltdc, (uint32_t)fb_address, LTDC_LAYER_1);
    __HAL_LTDC_LAYER_ENABLE(hltdc, LTDC_LAYER_1);
    HAL_DSI_Start(hdsi);
    lcd_refresh();
}

void lcd_clear_foreground() {
    memset(BACKBUFFER, 0xFF, sizeof(s_foreground_buffer_0));
}

void lcd_clear_area(unsigned int xl, unsigned int xr, unsigned int yb,
                    unsigned int yt) {
    // for (unsigned int xi = xl; xi <= xr; xi++) {
    //     for (unsigned int yi = yb; yi <= yt; yi++) {
    //         BACKBUFFER[yi + xi * LCD_HEIGHT] = 0xFF;
    //     }
    // }
    hdma2d.Init.Mode = DMA2D_R2M;
    hdma2d.Init.OutputOffset = LCD_HEIGHT - (yt - yb + 1);
    HAL_DMA2D_Init(&hdma2d);

    hdma2d.LayerCfg[0].InputOffset = 0;
    hdma2d.LayerCfg[0].InputColorMode = DMA2D_RGB565;
    hdma2d.LayerCfg[0].AlphaMode = DMA2D_NO_MODIF_ALPHA;
    hdma2d.LayerCfg[0].InputAlpha = 0xFF;
    HAL_DMA2D_ConfigLayer(&hdma2d, 0);

    HAL_DMA2D_Start(&hdma2d, 0xFFFFFFFF,
                    (uint32_t)&BACKBUFFER[yb + xl * LCD_HEIGHT], (yt - yb + 1),
                    (xr - xl + 1));
    HAL_DMA2D_PollForTransfer(&hdma2d, 100);
}

void lcd_draw_rectangle(unsigned int x, unsigned int y, unsigned int w,
                        unsigned int h, ColorRGB565 color) {
    // for (unsigned int xi = x; xi < x + w; xi++) {
    //     for (unsigned int yi = y; yi < y + h; yi++) {
    //         BACKBUFFER[yi + xi * LCD_HEIGHT] = color;
    //     }
    // }
    hdma2d.Init.Mode = DMA2D_R2M;
    hdma2d.Init.OutputOffset = LCD_HEIGHT - h;
    HAL_DMA2D_Init(&hdma2d);

    hdma2d.LayerCfg[0].InputOffset = 0;
    hdma2d.LayerCfg[0].InputColorMode = DMA2D_RGB565;
    hdma2d.LayerCfg[0].AlphaMode = DMA2D_NO_MODIF_ALPHA;
    hdma2d.LayerCfg[0].InputAlpha = 0xFF;
    HAL_DMA2D_ConfigLayer(&hdma2d, 0);

    HAL_DMA2D_Start(&hdma2d, (uint32_t)rgb565_to_rgb888(color),
                    (uint32_t)&BACKBUFFER[y + x * LCD_HEIGHT], h, w);
    HAL_DMA2D_PollForTransfer(&hdma2d, 100);
}

void lcd_draw_circle(unsigned int x, unsigned int y, unsigned int r,
                     ColorRGB565 color) {
    for (unsigned int xi = x - r; xi < x + r; xi++) {
        for (unsigned int yi = y - r; yi < y + r; yi++) {
            int dx = (int)xi - (int)x;
            int dy = (int)yi - (int)y;

            if ((unsigned int)(dx * dx + dy * dy) < r * r) {
                BACKBUFFER[yi + xi * LCD_HEIGHT] = color;
            }
        }
    }
}

void lcd_copy_background_to_foreground(const ColorRGB565* fb_address) {
    if (fb_address != NULL) {
        memcpy(BACKBUFFER, fb_address, sizeof(s_foreground_buffer_0));
    } else {
        memcpy(BACKBUFFER, (ColorRGB565*)hltdc->LayerCfg[0].FBStartAdress,
               sizeof(s_foreground_buffer_0));
    }
}

void lcd_set_foreground_alpha(uint8_t alpha) {
    HAL_LTDC_SetAlpha(hltdc, alpha, LTDC_LAYER_2);
    lcd_refresh();
}

void lcd_set_foreground_visibility(bool visible) {
    if (visible) {
        __HAL_LTDC_LAYER_ENABLE(hltdc, LTDC_LAYER_2);
    } else {
        __HAL_LTDC_LAYER_DISABLE(hltdc, LTDC_LAYER_2);
    }
    lcd_refresh();
}

void lcd_wait_for_vsync() {
    while ((hltdc->Instance->CPSR & 0xFFFF) >= LTDC_VSYNC &&
           (hltdc->Instance->CPSR & 0xFFFF) <
               (LTDC_VBP + LTDC_HEIGHT + LTDC_VSYNC - 2)) {
    }
}

unsigned int lcd_get_text_width(const Font* font, const char* str,
                                unsigned pt_size) {
    unsigned int width = 0;
    while (*str != '\0') {
        char ch = *str;
        str++;

        if (ch & 0x80) {
            continue;
        }

        const Glyph* glyph = font->glyphs[(uint8_t)ch];
        if (glyph->data == NULL) {
            continue;
        }

        width += glyph->advance * pt_size / font->width;
    }

    return width;
}

void lcd_draw_char(const Font* font, char ch, unsigned start_x,
                   unsigned start_y, unsigned pt_size, ColorRGB565 color,
                   unsigned int* advance) {
    if (advance) {
        *advance = 0;
    }

    if (ch & 0x80) {
        return;
    }

    const Glyph* glyph = font->glyphs[(uint8_t)ch];
    int width = font->width;
    int height = font->height;

    if (advance) {
        *advance = glyph->advance * pt_size / width;
    }

    if (glyph->data == NULL) {
        return;
    }

    for (int x = 0; x < (int)pt_size; x++) {
        for (int y = 0; y < (int)pt_size; y++) {
            int dest_x = (start_x + x);
            int dest_y = (start_y + pt_size - y);
            if (dest_y < 0 || dest_y >= LCD_HEIGHT || dest_x < 0 ||
                dest_x >= LCD_WIDTH) {
                continue;
            }

            // Determine texture coordinates
            int px = x * width / pt_size;
            int py = y * height / pt_size;

            int offset = px * height + py;
            int offset_byte = offset / 8;
            int offset_bit = offset % 8;

            bool subpixel =
                (glyph->data[offset_byte] & (0x1 << offset_bit)) != 0;
            if (subpixel) {
                BACKBUFFER[(start_y + pt_size - y) +
                           (start_x + x) * LCD_HEIGHT] = color;
            }
        }
    }
}

void lcd_draw_text(const Font* font, const char* str, unsigned start_x,
                   unsigned start_y, unsigned pt_size, ColorRGB565 color) {
    unsigned int cur_x = start_x;
    unsigned int advance = 0;
    while (*str != '\0') {
        lcd_draw_char(font, *str, cur_x, start_y, pt_size, color, &advance);
        cur_x += advance;
        str++;
    }
}

void lcd_end_of_refresh_callback(DSI_HandleTypeDef* hdsi) {
    // Frame rate tracking
    static unsigned int last_tick = 0;
    static unsigned int frame_count = 0;
    frame_count++;
    unsigned int current_tick = HAL_GetTick();
    if (frame_count >= 10) {
        unsigned int delta = current_tick - last_tick;
        unsigned int fps = (frame_count * 1000) / delta;
        printf("FPS: %u\n", fps);
        frame_count = 0;
        last_tick = current_tick;
    }

    // Done refreshing
    s_refreshing = false;
}

bool lcd_is_refreshing() {
    return s_refreshing;
}
