griffinross2/Topiary-TrimBot/firmware/src/M7/gui_app.cpp

#include "gui_app.h"

#include "lcd.h"
#include "gui.h"
#include "filesystem.h"
#include "timing.h"
#include "profiler.h"
#include "file_sender.h"
#include "pi_control.h"
#include "cross_section_manager.h"

#include "images/splashscreen.h"
#include "images/blank.h"
#include "images/main.h"
#include "images/file_send_error.h"
#include "images/begin_scanning.h"
#include "images/insert_card.h"
#include "images/cross_sections.h"
#include "images/begin_cutting.h"
#include "fonts/arial.h"
#include "graphics/arrow_up.h"
#include "graphics/arrow_down.h"
#include "graphics/loading0.h"
#include "graphics/loading1.h"
#include "graphics/loading2.h"
#include "graphics/loading3.h"
#include "graphics/loading4.h"
#include "graphics/loading5.h"
#include "graphics/loading6.h"
#include "graphics/loading7.h"

#include <algorithm>
#include <string>

static int s_init_status = STATUS_ERROR;

// Declare scene helpers
static Status load_splash_screen_scene();
static Status update_splash_screen_scene();
static Status load_file_list_scene();
static Status update_file_list(bool force_update = false);
static Status load_sending_file_scene();
static Status update_sending_file_scene();
static Status load_error_sending_file_scene();
static Status load_begin_scanning_scene();
static Status load_insert_card_scene();
static Status update_insert_card_scene();
static Status load_cross_section_scene();
static Status update_cross_section_scene();
static Status load_scanning_scene();
static Status update_scanning_scene();
static Status load_toolpathing_scene();
static Status update_toolpathing_scene();
static Status load_begin_cutting_scene();
static Status update_begin_cutting_scene();
static Status load_cutting_scene();
static Status update_cutting_scene();

/************************/
/* STARTUP SPLASHSCREEN */
/************************/

constexpr uint32_t splash_screen_scene_timeout = (2 * 60 * 1000);

static struct {
    Scene scene;
    uint32_t start_tick;
} s_splash_screen_scene_ctx;

static Status load_splash_screen_scene() {
    lcd_set_background(SPLASHSCREEN);

    gui_set_current_scene(&s_splash_screen_scene_ctx.scene);

    s_splash_screen_scene_ctx.start_tick = get_tick_ms();

    return STATUS_OK;
}

static Status update_splash_screen_scene() {
    if (pi_control_is_booted()) {
        if (s_init_status != STATUS_OK) {
            // If initialization failed, just show a blank screen
            lcd_set_background(BLANK);
            return STATUS_OK;
        } else {
            // Load the file list scene after the splash screen
            load_file_list_scene();
        }
    } else if (get_tick_ms() >= s_splash_screen_scene_ctx.start_tick +
                                    splash_screen_scene_timeout) {
        // If initialization failed, just show a blank screen
        lcd_set_background(BLANK);
        return STATUS_OK;
    }

    return STATUS_OK;
}

/*************************/
/* FILE SELECTION SCREEN */
/*************************/

#define MAX_FILES_DISPLAYED 6

static struct {
    bool initialized = false;
    Scene scene;
    std::vector<FileInfo> file_list;
    size_t selected_file_index = 0;
    size_t file_list_start_index = 0;
    size_t file_list_last_size = 0;
    long long unsigned last_update_tick;
    Button file_button[MAX_FILES_DISPLAYED];
    Label file_label[MAX_FILES_DISPLAYED];
    Label file_size_label[MAX_FILES_DISPLAYED];
    Rectangle file_divider[MAX_FILES_DISPLAYED];
    Button file_scroll_up_button;
    Button file_scroll_down_button;
    GraphicsObject file_scroll_up_graphic;
    GraphicsObject file_scroll_down_graphic;
    Rectangle dialog_border;
    Rectangle dialog_bg;
    Label dialog_label;
    Button dialog_confirm_button;
    Label dialog_confirm_label;
    Button dialog_cancel_button;
    Label dialog_cancel_label;
} s_file_list_scene_ctx;

static Status update_file_list(bool force_update) {
    PROFILER_ENTER();

    // If the SD card was removed close the dialog and switch to the insert card
    // scene
    if (!filesystem_is_card_inserted()) {
        s_file_list_scene_ctx.scene.set_dialog_active(false);
        load_insert_card_scene();
        PROFILER_EXIT();
        return STATUS_OK;
    }

    // Need to check if the file list changed or we scrolled
    // then update the text and or number of files displayed
    // Force update is true when the scroll button causes an update

    std::vector<FileInfo>& file_list = s_file_list_scene_ctx.file_list;

    std::vector<FileInfo> new_file_list;
    Status status = filesystem_get_file_list(new_file_list);

    // If the size changed, reset the scroll
    if (new_file_list.size() != s_file_list_scene_ctx.file_list_last_size) {
        s_file_list_scene_ctx.file_list_last_size = new_file_list.size();
        s_file_list_scene_ctx.file_list_start_index = 0;
    }

    // If the file list has become empty, close the dialog
    if (new_file_list.empty()) {
        s_file_list_scene_ctx.scene.set_dialog_active(false);
    }

    if (!force_update &&
        std::equal(file_list.begin(), file_list.end(), new_file_list.begin(),
                   new_file_list.end())) {
        // No change in file list, so we don't need to update
        PROFILER_EXIT();
        return STATUS_OK;
    }

    file_list = std::move(new_file_list);

    if (status != STATUS_OK) {
        PROFILER_EXIT();
        return status;
    }

    for (size_t i = 0; i < MAX_FILES_DISPLAYED; ++i) {
        // Check if this line should display a file or if we are out
        bool line_visible =
            i < file_list.size() - s_file_list_scene_ctx.file_list_start_index;

        if (!line_visible) {
            s_file_list_scene_ctx.file_button[i].set_visible(false);
            s_file_list_scene_ctx.file_label[i].set_visible(false);
            s_file_list_scene_ctx.file_size_label[i].set_visible(false);
            s_file_list_scene_ctx.file_divider[i].set_visible(false);
            continue;
        }

        size_t file_idx = s_file_list_scene_ctx.file_list_start_index + i;
        s_file_list_scene_ctx.file_label[i].set_text(file_list[file_idx].name);

        unsigned long long file_size = file_list[file_idx].size;
        char size_str[32];
        if (file_size >= 1024 * 1024) {
            snprintf(size_str, sizeof(size_str), "%.2f MB",
                     file_size / (1024.0 * 1024.0));
        } else if (file_size >= 1024) {
            snprintf(size_str, sizeof(size_str), "%.2f KB", file_size / 1024.0);
        } else {
            snprintf(size_str, sizeof(size_str), "%lu B",
                     (unsigned long)file_size);
        }

        s_file_list_scene_ctx.file_size_label[i].set_text(size_str);

        s_file_list_scene_ctx.file_button[i].set_visible(true);
        s_file_list_scene_ctx.file_label[i].set_visible(true);
        s_file_list_scene_ctx.file_size_label[i].set_visible(true);
        s_file_list_scene_ctx.file_divider[i].set_visible(true);
    }

    PROFILER_EXIT();
    return STATUS_OK;
};

static Status load_file_list_scene() {
    if (s_file_list_scene_ctx.initialized) {
        lcd_set_background(MAIN);
        gui_set_current_scene(&s_file_list_scene_ctx.scene);
        update_file_list(true);
        return STATUS_OK;
    }

    // Dialog box for confirming a file
    Scene& scene = s_file_list_scene_ctx.scene;
    Rectangle* dialog_border = &s_file_list_scene_ctx.dialog_border;
    Rectangle* dialog_bg = &s_file_list_scene_ctx.dialog_bg;
    Label* dialog_label = &s_file_list_scene_ctx.dialog_label;
    Button* dialog_confirm_button =
        &s_file_list_scene_ctx.dialog_confirm_button;
    Label* dialog_confirm_label = &s_file_list_scene_ctx.dialog_confirm_label;
    Button* dialog_cancel_button = &s_file_list_scene_ctx.dialog_cancel_button;
    Label* dialog_cancel_label = &s_file_list_scene_ctx.dialog_cancel_label;
    constexpr int dialog_width = 400;
    constexpr int dialog_height = 120;
    constexpr int dialog_border_thickness = 2;

    *dialog_border = Rectangle(
        &scene, WINDOW_WIDTH / 2 - dialog_width / 2 - dialog_border_thickness,
        WINDOW_HEIGHT / 2 - dialog_height / 2 - dialog_border_thickness,
        dialog_width + dialog_border_thickness * 2,
        dialog_height + dialog_border_thickness * 2, 0xF1);
    *dialog_bg = Rectangle(&scene, WINDOW_WIDTH / 2 - dialog_width / 2,
                           WINDOW_HEIGHT / 2 - dialog_height / 2, dialog_width,
                           dialog_height, 0xF0);

    *dialog_label =
        Label(&scene, WINDOW_WIDTH / 2, WINDOW_HEIGHT / 2 + 5, "", 32);
    dialog_label->set_alignment(LABEL_ALIGN_CENTER);

    *dialog_confirm_button = Button(&scene, WINDOW_WIDTH / 2 + 10,
                                    WINDOW_HEIGHT / 2 - dialog_height / 3,
                                    dialog_width / 3, dialog_height / 3);

    *dialog_confirm_label =
        Label(&scene, WINDOW_WIDTH / 2 + dialog_width / 6 + 10,
              WINDOW_HEIGHT / 2 - dialog_height / 3 + 2, "OK", 32);
    dialog_confirm_label->set_alignment(LABEL_ALIGN_CENTER);

    dialog_confirm_button->set_on_click([](int x, int y) {
        // Send file if the index is still valid (card wasn't removed)
        if (s_file_list_scene_ctx.selected_file_index <
            s_file_list_scene_ctx.file_list.size()) {
            const FileInfo& selected_file =
                s_file_list_scene_ctx
                    .file_list[s_file_list_scene_ctx.selected_file_index];
            file_sender_send_file(selected_file.name.c_str());
            TRACE_PRINTF("Sending file: %s\n", selected_file.name.c_str());

            // Go to file sending screen
            load_sending_file_scene();
        }

        s_file_list_scene_ctx.scene.set_dialog_active(false);
    });

    *dialog_cancel_button =
        Button(&scene, WINDOW_WIDTH / 2 - dialog_width / 3 - 10,
               WINDOW_HEIGHT / 2 - dialog_height / 3, dialog_width / 3,
               dialog_height / 3);

    *dialog_cancel_label =
        Label(&scene, WINDOW_WIDTH / 2 - dialog_width / 6 - 10,
              WINDOW_HEIGHT / 2 - dialog_height / 3 + 2, "Cancel", 32);
    dialog_cancel_label->set_alignment(LABEL_ALIGN_CENTER);

    dialog_cancel_button->set_on_click([](int x, int y) {
        s_file_list_scene_ctx.scene.set_dialog_active(false);
    });

    scene.add_dialog_object(dialog_border);
    scene.add_dialog_object(dialog_bg);
    scene.add_dialog_object(dialog_label);
    scene.add_dialog_object(dialog_confirm_button);
    scene.add_dialog_object(dialog_confirm_label);
    scene.add_dialog_object(dialog_cancel_button);
    scene.add_dialog_object(dialog_cancel_label);

    // Static file list components
    s_file_list_scene_ctx.file_scroll_up_button =
        Button(&scene, WINDOW_WIDTH - 80, WINDOW_HEIGHT - 40 - 10, 40, 40);
    s_file_list_scene_ctx.file_scroll_up_button.set_on_click([](int x, int y) {
        if (s_file_list_scene_ctx.file_list_start_index > 0) {
            s_file_list_scene_ctx.file_list_start_index--;
            update_file_list(true);
        }
    });
    s_file_list_scene_ctx.file_scroll_up_button.bg_off();

    s_file_list_scene_ctx.file_scroll_down_button =
        Button(&scene, WINDOW_WIDTH - 80, 10, 40, 40);
    s_file_list_scene_ctx.file_scroll_down_button.set_on_click([](int x,
                                                                  int y) {
        if (s_file_list_scene_ctx.file_list_start_index + MAX_FILES_DISPLAYED <
            s_file_list_scene_ctx.file_list.size()) {
            s_file_list_scene_ctx.file_list_start_index++;
            update_file_list(true);
        }
    });
    s_file_list_scene_ctx.file_scroll_down_button.bg_off();

    s_file_list_scene_ctx.file_scroll_up_graphic = GraphicsObject(
        &scene, ARROW_UP, WINDOW_WIDTH - 80, WINDOW_HEIGHT - 40 - 10);

    s_file_list_scene_ctx.file_scroll_down_graphic =
        GraphicsObject(&scene, ARROW_DOWN, WINDOW_WIDTH - 80, 10);

    scene.add_object(&s_file_list_scene_ctx.file_scroll_up_button);
    scene.add_object(&s_file_list_scene_ctx.file_scroll_down_button);
    scene.add_object(&s_file_list_scene_ctx.file_scroll_up_graphic);
    scene.add_object(&s_file_list_scene_ctx.file_scroll_down_graphic);

    // Add in the file list
    for (size_t i = 0; i < MAX_FILES_DISPLAYED; ++i) {
        s_file_list_scene_ctx.file_button[i] = Button(
            &scene, 40, WINDOW_HEIGHT - 48 - i * 48, WINDOW_WIDTH - 130, 48);
        s_file_list_scene_ctx.file_button[i].bg_off();
        s_file_list_scene_ctx.file_button[i].set_on_click([scene, i](int x,
                                                                     int y) {
            size_t file_idx = s_file_list_scene_ctx.file_list_start_index + i;
            s_file_list_scene_ctx.selected_file_index = file_idx;
            s_file_list_scene_ctx.dialog_label.set_text(
                "Send " + s_file_list_scene_ctx.file_list[file_idx].name + "?");
            s_file_list_scene_ctx.scene.set_dialog_active(true);
        });

        s_file_list_scene_ctx.file_label[i] =
            Label(&scene, 50, WINDOW_HEIGHT - 48 - i * 48, "", 32);

        s_file_list_scene_ctx.file_divider[i] =
            Rectangle(&scene, 50, WINDOW_HEIGHT - 48 - i * 48 - 4,
                      WINDOW_WIDTH - 150, 2, 0xFA);

        s_file_list_scene_ctx.file_size_label[i] = Label(
            &scene, WINDOW_WIDTH - 105, WINDOW_HEIGHT - 48 - i * 48, "", 32);
        s_file_list_scene_ctx.file_size_label[i].set_alignment(
            LABEL_ALIGN_RIGHT);

        // Invisible by default
        s_file_list_scene_ctx.file_button[i].set_visible(false);
        s_file_list_scene_ctx.file_label[i].set_visible(false);
        s_file_list_scene_ctx.file_divider[i].set_visible(false);
        s_file_list_scene_ctx.file_size_label[i].set_visible(false);

        scene.add_object(&s_file_list_scene_ctx.file_button[i]);
        scene.add_object(&s_file_list_scene_ctx.file_label[i]);
        scene.add_object(&s_file_list_scene_ctx.file_divider[i]);
        scene.add_object(&s_file_list_scene_ctx.file_size_label[i]);
    }

    // Update the list objects
    update_file_list();

    lcd_set_background(MAIN);
    gui_set_current_scene(&scene);

    s_file_list_scene_ctx.initialized = true;

    return STATUS_OK;
}

/***********************/
/* SENDING FILE SCREEN */
/***********************/

static struct {
    bool initialized = false;
    Scene scene;
    Label status_label;
    GraphicsObject spinner;
    size_t animation_idx = 0;
    long long unsigned last_update_tick;
} s_sending_file_scene_ctx;

static Status load_sending_file_scene() {
    if (s_sending_file_scene_ctx.initialized) {
        lcd_set_background(MAIN);
        gui_set_current_scene(&s_sending_file_scene_ctx.scene);
        return STATUS_OK;
    }

    Scene& scene = s_sending_file_scene_ctx.scene;
    Label& status_label = s_sending_file_scene_ctx.status_label;
    GraphicsObject& spinner = s_sending_file_scene_ctx.spinner;

    status_label = Label(&scene, WINDOW_WIDTH / 2, WINDOW_HEIGHT / 2 + 20,
                         "Sending file...", 32);
    status_label.set_alignment(LABEL_ALIGN_CENTER);

    spinner =
        GraphicsObject(&scene, LOADING0, WINDOW_WIDTH / 2 - LOADING0.width / 2,
                       WINDOW_HEIGHT / 2 - 20 - LOADING0.height);

    scene.add_object(&spinner);
    scene.add_object(&status_label);

    lcd_set_background(MAIN);
    gui_set_current_scene(&scene);

    s_sending_file_scene_ctx.initialized = true;

    return STATUS_OK;
}

static Status update_sending_file_scene() {
    // Go to error screen if the file sender is in the error state
    if (file_sender_get_status() == FILE_SENDER_STATUS_ERROR) {
        file_sender_reset();
        load_error_sending_file_scene();
        return STATUS_OK;
    }

    // Go to the scanning confirmation screen if the file sender is done
    if (file_sender_get_status() == FILE_SENDER_STATUS_SUCCESS) {
        file_sender_reset();
        load_begin_scanning_scene();
        return STATUS_OK;
    }

    // Looping 8-frame animation
    s_sending_file_scene_ctx.animation_idx =
        (s_sending_file_scene_ctx.animation_idx + 1) % 8;

    switch (s_sending_file_scene_ctx.animation_idx) {
        case 0:
            s_sending_file_scene_ctx.spinner.set_graphics(LOADING0);
            break;
        case 1:
            s_sending_file_scene_ctx.spinner.set_graphics(LOADING1);
            break;
        case 2:
            s_sending_file_scene_ctx.spinner.set_graphics(LOADING2);
            break;
        case 3:
            s_sending_file_scene_ctx.spinner.set_graphics(LOADING3);
            break;
        case 4:
            s_sending_file_scene_ctx.spinner.set_graphics(LOADING4);
            break;
        case 5:
            s_sending_file_scene_ctx.spinner.set_graphics(LOADING5);
            break;
        case 6:
            s_sending_file_scene_ctx.spinner.set_graphics(LOADING6);
            break;
        case 7:
            s_sending_file_scene_ctx.spinner.set_graphics(LOADING7);
            break;
        default:
            break;
    }

    return STATUS_OK;
}

/*****************************/
/* ERROR SENDING FILE SCREEN */
/*****************************/

static struct {
    bool initialized = false;
    Scene scene;
    Button back_button;
    Label back_label;
} s_error_sending_file_scene_ctx;

constexpr unsigned int BACK_BUTTON_WIDTH = 150;
constexpr unsigned int BACK_BUTTON_HEIGHT = 60;
constexpr unsigned int BACK_TEXT_SIZE = 32;

static Status load_error_sending_file_scene() {
    if (s_error_sending_file_scene_ctx.initialized) {
        lcd_set_background(FILE_SEND_ERROR);
        gui_set_current_scene(&s_error_sending_file_scene_ctx.scene);
        return STATUS_OK;
    }

    Scene& scene = s_error_sending_file_scene_ctx.scene;
    Button& back_button = s_error_sending_file_scene_ctx.back_button;
    Label& back_label = s_error_sending_file_scene_ctx.back_label;

    back_button = Button(&scene, WINDOW_WIDTH / 2 - BACK_BUTTON_WIDTH / 2, 0,
                         BACK_BUTTON_WIDTH, BACK_BUTTON_HEIGHT);
    back_button.set_on_click([](int x, int y) { load_file_list_scene(); });

    back_label = Label(&scene, WINDOW_WIDTH / 2,
                       BACK_BUTTON_HEIGHT / 2 - BACK_TEXT_SIZE / 2, "Back",
                       BACK_TEXT_SIZE);
    back_label.set_alignment(LABEL_ALIGN_CENTER);

    scene.add_object(&back_button);
    scene.add_object(&back_label);

    lcd_set_background(FILE_SEND_ERROR);
    gui_set_current_scene(&scene);

    s_error_sending_file_scene_ctx.initialized = true;

    return STATUS_OK;
}

/*************************/
/* BEGIN SCANNING SCREEN */
/*************************/

static struct {
    bool initialized = false;
    Scene scene;
    Button cancel_button;
    Label cancel_label;
    Button confirm_button;
    Label confirm_label;
} s_begin_scanning_scene_ctx;

constexpr unsigned int BEGIN_SCANNING_BUTTON_WIDTH = 150;
constexpr unsigned int BEGIN_SCANNING_BUTTON_HEIGHT = 60;
constexpr unsigned int BEGIN_SCANNING_TEXT_SIZE = 32;

static Status load_begin_scanning_scene() {
    if (s_begin_scanning_scene_ctx.initialized) {
        lcd_set_background(BEGIN_SCANNING);
        gui_set_current_scene(&s_begin_scanning_scene_ctx.scene);
        return STATUS_OK;
    }

    Scene& scene = s_begin_scanning_scene_ctx.scene;
    Button& cancel_button = s_begin_scanning_scene_ctx.cancel_button;
    Label& cancel_label = s_begin_scanning_scene_ctx.cancel_label;
    Button& confirm_button = s_begin_scanning_scene_ctx.confirm_button;
    Label& confirm_label = s_begin_scanning_scene_ctx.confirm_label;

    cancel_button =
        Button(&scene, WINDOW_WIDTH / 2 - BEGIN_SCANNING_BUTTON_WIDTH - 10, 0,
               BEGIN_SCANNING_BUTTON_WIDTH, BEGIN_SCANNING_BUTTON_HEIGHT);
    cancel_button.set_on_click([](int x, int y) { load_file_list_scene(); });

    cancel_label =
        Label(&scene, WINDOW_WIDTH / 2 - BEGIN_SCANNING_BUTTON_WIDTH / 2 - 10,
              BEGIN_SCANNING_BUTTON_HEIGHT / 2 - BEGIN_SCANNING_TEXT_SIZE / 2,
              "Cancel", BEGIN_SCANNING_TEXT_SIZE);
    cancel_label.set_alignment(LABEL_ALIGN_CENTER);

    confirm_button =
        Button(&scene, WINDOW_WIDTH / 2 + 10, 0, BEGIN_SCANNING_BUTTON_WIDTH,
               BEGIN_SCANNING_BUTTON_HEIGHT);
    confirm_button.set_on_click([](int x, int y) {
        pi_control_start_scanning();
        load_scanning_scene();
    });

    confirm_label =
        Label(&scene, WINDOW_WIDTH / 2 + BEGIN_SCANNING_BUTTON_WIDTH / 2 + 10,
              BEGIN_SCANNING_BUTTON_HEIGHT / 2 - BEGIN_SCANNING_TEXT_SIZE / 2,
              "Confirm", BEGIN_SCANNING_TEXT_SIZE);
    confirm_label.set_alignment(LABEL_ALIGN_CENTER);

    scene.add_object(&cancel_button);
    scene.add_object(&cancel_label);
    scene.add_object(&confirm_button);
    scene.add_object(&confirm_label);

    lcd_set_background(BEGIN_SCANNING);
    gui_set_current_scene(&scene);

    s_begin_scanning_scene_ctx.initialized = true;

    return STATUS_OK;
}

/**********************/
/* INSERT CARD SCREEN */
/**********************/

static struct {
    Scene scene;
} s_insert_card_scene_ctx;

static Status load_insert_card_scene() {
    lcd_set_background(INSERT_CARD);
    gui_set_current_scene(&s_insert_card_scene_ctx.scene);

    return STATUS_OK;
}

static Status update_insert_card_scene() {
    // If the card is inserted, go to the file list scene
    if (filesystem_is_card_inserted() && filesystem_is_mounted()) {
        load_file_list_scene();
    }

    return STATUS_OK;
}

/*****************/
/* SLICER SCREEN */
/*****************/

static struct {
    bool initialized = false;
    Scene scene;
    uint8_t current_layer = CROSS_SECTION_NUM_SLICES / 2;
    Button up_button;
    Button down_button;
    GraphicsObject up_arrow;
    GraphicsObject down_arrow;
    Label layer_label;
    char layer_label_buf[4];
    Button confirm_button;
    Label confirm_label;
} s_cross_section_scene_ctx;

static Status load_cross_section_scene() {
    if (s_cross_section_scene_ctx.initialized) {
        lcd_set_background(CROSS_SECTIONS);
        gui_set_current_scene(&s_cross_section_scene_ctx.scene);
        return STATUS_OK;
    }

    Scene& scene = s_cross_section_scene_ctx.scene;

    // Up and down buttons to change layer
    s_cross_section_scene_ctx.up_button = Button(&scene, 254, 226, 40, 40);
    s_cross_section_scene_ctx.up_button.set_on_click([](int x, int y) {
        if (s_cross_section_scene_ctx.current_layer <
            CROSS_SECTION_NUM_SLICES - 1) {
            s_cross_section_scene_ctx.current_layer++;
            cross_section_manager_get_layer(
                s_cross_section_scene_ctx.current_layer);
            snprintf(s_cross_section_scene_ctx.layer_label_buf,
                     sizeof(s_cross_section_scene_ctx.layer_label_buf), "%d",
                     s_cross_section_scene_ctx.current_layer);
            s_cross_section_scene_ctx.layer_label.set_text(
                s_cross_section_scene_ctx.layer_label_buf);
        }
    });

    s_cross_section_scene_ctx.down_button = Button(&scene, 254, 162, 40, 40);
    s_cross_section_scene_ctx.down_button.set_on_click([](int x, int y) {
        if (s_cross_section_scene_ctx.current_layer > 0) {
            s_cross_section_scene_ctx.current_layer--;
            cross_section_manager_get_layer(
                s_cross_section_scene_ctx.current_layer);
            snprintf(s_cross_section_scene_ctx.layer_label_buf,
                     sizeof(s_cross_section_scene_ctx.layer_label_buf), "%d",
                     s_cross_section_scene_ctx.current_layer);
            s_cross_section_scene_ctx.layer_label.set_text(
                s_cross_section_scene_ctx.layer_label_buf);
        }
    });

    // Arrows for the buttons
    s_cross_section_scene_ctx.up_arrow =
        GraphicsObject(&scene, ARROW_UP, 254, 226);
    s_cross_section_scene_ctx.down_arrow =
        GraphicsObject(&scene, ARROW_DOWN, 254, 162);

    scene.add_object(&s_cross_section_scene_ctx.up_button);
    scene.add_object(&s_cross_section_scene_ctx.down_button);
    scene.add_object(&s_cross_section_scene_ctx.up_arrow);
    scene.add_object(&s_cross_section_scene_ctx.down_arrow);

    // Label to show the current layer
    snprintf(s_cross_section_scene_ctx.layer_label_buf,
             sizeof(s_cross_section_scene_ctx.layer_label_buf), "%d",
             s_cross_section_scene_ctx.current_layer);
    s_cross_section_scene_ctx.layer_label =
        Label(&scene, 331, 289, s_cross_section_scene_ctx.layer_label_buf, 16);
    s_cross_section_scene_ctx.layer_label.set_alignment(LABEL_ALIGN_RIGHT);

    scene.add_object(&s_cross_section_scene_ctx.layer_label);

    // Confirm button to start scanning
    s_cross_section_scene_ctx.confirm_button = Button(&scene, 117, 20, 175, 40);
    s_cross_section_scene_ctx.confirm_button.set_on_click([](int x, int y) {
        load_toolpathing_scene();
        pi_control_start_toolpathing();
    });

    // Confirm label
    s_cross_section_scene_ctx.confirm_label =
        Label(&scene, 117 + 175 / 2, 20 + 40 / 2 - 16, "Confirm", 32);
    s_cross_section_scene_ctx.confirm_label.set_alignment(LABEL_ALIGN_CENTER);

    scene.add_object(&s_cross_section_scene_ctx.confirm_button);
    scene.add_object(&s_cross_section_scene_ctx.confirm_label);

    // Ask the Pi to generate the cross sections
    cross_section_manager_create_cross_sections(CROSS_SECTION_NUM_SLICES);

    // Ask for the first cross section
    cross_section_manager_get_layer(CROSS_SECTION_NUM_SLICES / 2);

    // Add all of the line objects
    size_t num_plant_lines = cross_section_manager_get_num_plant_lines();
    Line* plant_lines = cross_section_manager_get_plant_lines();
    for (size_t i = 0; i < num_plant_lines; i++) {
        scene.add_object(&plant_lines[i]);
    }
    size_t num_model_lines = cross_section_manager_get_num_model_lines();
    Line* model_lines = cross_section_manager_get_model_lines();
    for (size_t i = 0; i < num_model_lines; i++) {
        scene.add_object(&model_lines[i]);
    }

    lcd_set_background(CROSS_SECTIONS);
    gui_set_current_scene(&scene);

    s_cross_section_scene_ctx.initialized = true;

    return STATUS_OK;
}

static Status update_cross_section_scene() {
    return STATUS_OK;
}

/*******************/
/* SCANNING SCREEN */
/*******************/

static struct {
    bool initialized = false;
    Scene scene;
    Label status_label;
    GraphicsObject spinner;
    size_t animation_idx = 0;
    long long unsigned last_update_tick;
} s_scanning_scene_ctx;

static Status load_scanning_scene() {
    if (s_scanning_scene_ctx.initialized) {
        lcd_set_background(MAIN);
        gui_set_current_scene(&s_scanning_scene_ctx.scene);
        return STATUS_OK;
    }

    Scene& scene = s_scanning_scene_ctx.scene;
    Label& status_label = s_scanning_scene_ctx.status_label;
    GraphicsObject& spinner = s_scanning_scene_ctx.spinner;

    status_label = Label(&scene, WINDOW_WIDTH / 2, WINDOW_HEIGHT / 2 + 20,
                         "Scanning...", 32);
    status_label.set_alignment(LABEL_ALIGN_CENTER);

    spinner =
        GraphicsObject(&scene, LOADING0, WINDOW_WIDTH / 2 - LOADING0.width / 2,
                       WINDOW_HEIGHT / 2 - 20 - LOADING0.height);

    scene.add_object(&spinner);
    scene.add_object(&status_label);

    lcd_set_background(MAIN);
    gui_set_current_scene(&scene);

    s_scanning_scene_ctx.initialized = true;

    return STATUS_OK;
}

static Status update_scanning_scene() {
    // If scanning is done, go to the cross section screen
    if (!pi_control_is_scanning()) {
        load_cross_section_scene();
        return STATUS_OK;
    }

    // Looping 8-frame animation
    s_scanning_scene_ctx.animation_idx =
        (s_scanning_scene_ctx.animation_idx + 1) % 8;

    switch (s_scanning_scene_ctx.animation_idx) {
        case 0:
            s_scanning_scene_ctx.spinner.set_graphics(LOADING0);
            break;
        case 1:
            s_scanning_scene_ctx.spinner.set_graphics(LOADING1);
            break;
        case 2:
            s_scanning_scene_ctx.spinner.set_graphics(LOADING2);
            break;
        case 3:
            s_scanning_scene_ctx.spinner.set_graphics(LOADING3);
            break;
        case 4:
            s_scanning_scene_ctx.spinner.set_graphics(LOADING4);
            break;
        case 5:
            s_scanning_scene_ctx.spinner.set_graphics(LOADING5);
            break;
        case 6:
            s_scanning_scene_ctx.spinner.set_graphics(LOADING6);
            break;
        case 7:
            s_scanning_scene_ctx.spinner.set_graphics(LOADING7);
            break;
        default:
            break;
    }

    return STATUS_OK;
}

/**********************/
/* TOOLPATHING SCREEN */
/**********************/

static struct {
    bool initialized = false;
    Scene scene;
    Label status_label;
    GraphicsObject spinner;
    size_t animation_idx = 0;
    long long unsigned last_update_tick;
} s_toolpathing_scene_ctx;

static Status load_toolpathing_scene() {
    if (s_toolpathing_scene_ctx.initialized) {
        lcd_set_background(MAIN);
        gui_set_current_scene(&s_toolpathing_scene_ctx.scene);
        return STATUS_OK;
    }

    Scene& scene = s_toolpathing_scene_ctx.scene;
    Label& status_label = s_toolpathing_scene_ctx.status_label;
    GraphicsObject& spinner = s_toolpathing_scene_ctx.spinner;

    status_label = Label(&scene, WINDOW_WIDTH / 2, WINDOW_HEIGHT / 2 + 20,
                         "Toolpathing...", 32);
    status_label.set_alignment(LABEL_ALIGN_CENTER);

    spinner =
        GraphicsObject(&scene, LOADING0, WINDOW_WIDTH / 2 - LOADING0.width / 2,
                       WINDOW_HEIGHT / 2 - 20 - LOADING0.height);

    scene.add_object(&spinner);
    scene.add_object(&status_label);

    lcd_set_background(MAIN);
    gui_set_current_scene(&scene);

    s_toolpathing_scene_ctx.initialized = true;

    return STATUS_OK;
}

static Status update_toolpathing_scene() {
    // If toolpathing is done, go to the cross section screen
    if (!pi_control_is_toolpathing()) {
        load_begin_cutting_scene();
        return STATUS_OK;
    }

    // Looping 8-frame animation
    s_toolpathing_scene_ctx.animation_idx =
        (s_toolpathing_scene_ctx.animation_idx + 1) % 8;

    switch (s_toolpathing_scene_ctx.animation_idx) {
        case 0:
            s_toolpathing_scene_ctx.spinner.set_graphics(LOADING0);
            break;
        case 1:
            s_toolpathing_scene_ctx.spinner.set_graphics(LOADING1);
            break;
        case 2:
            s_toolpathing_scene_ctx.spinner.set_graphics(LOADING2);
            break;
        case 3:
            s_toolpathing_scene_ctx.spinner.set_graphics(LOADING3);
            break;
        case 4:
            s_toolpathing_scene_ctx.spinner.set_graphics(LOADING4);
            break;
        case 5:
            s_toolpathing_scene_ctx.spinner.set_graphics(LOADING5);
            break;
        case 6:
            s_toolpathing_scene_ctx.spinner.set_graphics(LOADING6);
            break;
        case 7:
            s_toolpathing_scene_ctx.spinner.set_graphics(LOADING7);
            break;
        default:
            break;
    }

    return STATUS_OK;
}

/************************/
/* BEGIN CUTTING SCREEN */
/************************/

static struct {
    bool initialized = false;
    Scene scene;
    Button cancel_button;
    Label cancel_label;
    Button confirm_button;
    Label confirm_label;
} s_begin_cutting_scene_ctx;

constexpr unsigned int BEGIN_CUTTING_BUTTON_WIDTH = 150;
constexpr unsigned int BEGIN_CUTTING_BUTTON_HEIGHT = 60;
constexpr unsigned int BEGIN_CUTTING_TEXT_SIZE = 32;

static Status load_begin_cutting_scene() {
    if (s_begin_cutting_scene_ctx.initialized) {
        lcd_set_background(BEGIN_CUTTING);
        gui_set_current_scene(&s_begin_cutting_scene_ctx.scene);
        return STATUS_OK;
    }

    Scene& scene = s_begin_cutting_scene_ctx.scene;
    Button& cancel_button = s_begin_cutting_scene_ctx.cancel_button;
    Label& cancel_label = s_begin_cutting_scene_ctx.cancel_label;
    Button& confirm_button = s_begin_cutting_scene_ctx.confirm_button;
    Label& confirm_label = s_begin_cutting_scene_ctx.confirm_label;

    cancel_button =
        Button(&scene, WINDOW_WIDTH / 2 - BEGIN_CUTTING_BUTTON_WIDTH - 10, 0,
               BEGIN_CUTTING_BUTTON_WIDTH, BEGIN_CUTTING_BUTTON_HEIGHT);
    cancel_button.set_on_click([](int x, int y) { load_file_list_scene(); });

    cancel_label =
        Label(&scene, WINDOW_WIDTH / 2 - BEGIN_CUTTING_BUTTON_WIDTH / 2 - 10,
              BEGIN_CUTTING_BUTTON_HEIGHT / 2 - BEGIN_CUTTING_TEXT_SIZE / 2,
              "Cancel", BEGIN_CUTTING_TEXT_SIZE);
    cancel_label.set_alignment(LABEL_ALIGN_CENTER);

    confirm_button =
        Button(&scene, WINDOW_WIDTH / 2 + 10, 0, BEGIN_CUTTING_BUTTON_WIDTH,
               BEGIN_CUTTING_BUTTON_HEIGHT);
    confirm_button.set_on_click([](int x, int y) {
        pi_control_start_cutting();
        load_cutting_scene();
    });

    confirm_label =
        Label(&scene, WINDOW_WIDTH / 2 + BEGIN_CUTTING_BUTTON_WIDTH / 2 + 10,
              BEGIN_CUTTING_BUTTON_HEIGHT / 2 - BEGIN_CUTTING_TEXT_SIZE / 2,
              "Confirm", BEGIN_CUTTING_TEXT_SIZE);
    confirm_label.set_alignment(LABEL_ALIGN_CENTER);

    scene.add_object(&cancel_button);
    scene.add_object(&cancel_label);
    scene.add_object(&confirm_button);
    scene.add_object(&confirm_label);

    lcd_set_background(BEGIN_CUTTING);
    gui_set_current_scene(&scene);

    s_begin_cutting_scene_ctx.initialized = true;

    return STATUS_OK;
}

static Status update_begin_cutting_scene() {
    return STATUS_OK;
}

/******************/
/* CUTTING SCREEN */
/******************/

static struct {
    bool initialized = false;
    Scene scene;
    Label status_label;
    GraphicsObject spinner;
    size_t animation_idx = 0;
    long long unsigned last_update_tick;
} s_cutting_scene_ctx;

static Status load_cutting_scene() {
    if (s_cutting_scene_ctx.initialized) {
        lcd_set_background(MAIN);
        gui_set_current_scene(&s_cutting_scene_ctx.scene);
        return STATUS_OK;
    }

    Scene& scene = s_cutting_scene_ctx.scene;
    Label& status_label = s_cutting_scene_ctx.status_label;
    GraphicsObject& spinner = s_cutting_scene_ctx.spinner;

    status_label = Label(&scene, WINDOW_WIDTH / 2, WINDOW_HEIGHT / 2 + 20,
                         "Cutting...", 32);
    status_label.set_alignment(LABEL_ALIGN_CENTER);

    spinner =
        GraphicsObject(&scene, LOADING0, WINDOW_WIDTH / 2 - LOADING0.width / 2,
                       WINDOW_HEIGHT / 2 - 20 - LOADING0.height);

    scene.add_object(&spinner);
    scene.add_object(&status_label);

    lcd_set_background(MAIN);
    gui_set_current_scene(&scene);

    s_cutting_scene_ctx.initialized = true;

    return STATUS_OK;
}

static Status update_cutting_scene() {
    // If cutting is done, go back to the file screen
    if (!pi_control_is_cutting()) {
        load_file_list_scene();
        return STATUS_OK;
    }

    // Looping 8-frame animation
    s_cutting_scene_ctx.animation_idx =
        (s_cutting_scene_ctx.animation_idx + 1) % 8;

    switch (s_cutting_scene_ctx.animation_idx) {
        case 0:
            s_cutting_scene_ctx.spinner.set_graphics(LOADING0);
            break;
        case 1:
            s_cutting_scene_ctx.spinner.set_graphics(LOADING1);
            break;
        case 2:
            s_cutting_scene_ctx.spinner.set_graphics(LOADING2);
            break;
        case 3:
            s_cutting_scene_ctx.spinner.set_graphics(LOADING3);
            break;
        case 4:
            s_cutting_scene_ctx.spinner.set_graphics(LOADING4);
            break;
        case 5:
            s_cutting_scene_ctx.spinner.set_graphics(LOADING5);
            break;
        case 6:
            s_cutting_scene_ctx.spinner.set_graphics(LOADING6);
            break;
        case 7:
            s_cutting_scene_ctx.spinner.set_graphics(LOADING7);
            break;
        default:
            break;
    }

    return STATUS_OK;
}

Status gui_app_init() {
    lcd_set_background(BLANK);
    lcd_clear_foreground();
    lcd_swap_buffers();

    load_splash_screen_scene();

    return STATUS_OK;
}

void gui_app_init_status(int status) {
    s_init_status = status;
}

void gui_app_task() {
    PROFILER_ENTER();

    static uint32_t last_fps_check = HAL_GetTick();
    static int num_frames = 0;

    // Scene specific updates

    // Splash screen
    if (gui_get_current_scene() == &s_splash_screen_scene_ctx.scene) {
        update_splash_screen_scene();
    }

    // File list
    if (gui_get_current_scene() == &s_file_list_scene_ctx.scene) {
        if (get_tick_ms() - s_file_list_scene_ctx.last_update_tick >= 1000) {
            update_file_list();
            s_file_list_scene_ctx.last_update_tick = get_tick_ms();
        }
    }

    // Sending file screen
    if (gui_get_current_scene() == &s_sending_file_scene_ctx.scene) {
        if (get_tick_ms() - s_sending_file_scene_ctx.last_update_tick >= 200) {
            update_sending_file_scene();
            s_sending_file_scene_ctx.last_update_tick = get_tick_ms();
        }
    }

    // Insert card screen
    if (gui_get_current_scene() == &s_insert_card_scene_ctx.scene) {
        update_insert_card_scene();
    }

    // Cross section screen
    if (gui_get_current_scene() == &s_cross_section_scene_ctx.scene) {
        update_cross_section_scene();
    }

    // Scanning screen
    if (gui_get_current_scene() == &s_scanning_scene_ctx.scene) {
        if (get_tick_ms() - s_scanning_scene_ctx.last_update_tick >= 200) {
            update_scanning_scene();
            s_scanning_scene_ctx.last_update_tick = get_tick_ms();
        }
    }

    // Toolpathing screen
    if (gui_get_current_scene() == &s_toolpathing_scene_ctx.scene) {
        if (get_tick_ms() - s_toolpathing_scene_ctx.last_update_tick >= 200) {
            update_toolpathing_scene();
            s_toolpathing_scene_ctx.last_update_tick = get_tick_ms();
        }
    }

    // Begin cutting screen
    if (gui_get_current_scene() == &s_begin_cutting_scene_ctx.scene) {
        update_begin_cutting_scene();
    }

    // Cutting screen
    if (gui_get_current_scene() == &s_cutting_scene_ctx.scene) {
        if (get_tick_ms() - s_cutting_scene_ctx.last_update_tick >= 200) {
            update_cutting_scene();
            s_cutting_scene_ctx.last_update_tick = get_tick_ms();
        }
    }

    // Global update
    gui_update();
    gui_render();

    num_frames++;

    // Print framerate
    if (HAL_GetTick() - last_fps_check >= 5000) {
        float fps = 1000.0f * num_frames / (HAL_GetTick() - last_fps_check);
        printf("FPS: %.2f\n", fps);
        last_fps_check = HAL_GetTick();
        num_frames = 0;
    }

    PROFILER_EXIT();
}
