griffinross2/Topiary-TrimBot/experimental/lcd_prototyping_platformio/src/flash.c

#include "flash.h"

#include "stm32f4xx_hal.h"

#include <stdio.h>
#include <string.h>

QSPI_HandleTypeDef hqspi;

static const QSPI_CommandTypeDef s_qspi_default_cmd_1_line = {
    .Address = 0,
    .AddressMode = QSPI_ADDRESS_1_LINE,
    .AddressSize = QSPI_ADDRESS_24_BITS,
    .AlternateByteMode = QSPI_ALTERNATE_BYTES_NONE,
    .AlternateBytes = 0,
    .AlternateBytesSize = 0,
    .DataMode = QSPI_DATA_1_LINE,
    .DdrHoldHalfCycle = 0,
    .DdrMode = QSPI_DDR_MODE_DISABLE,
    .DummyCycles = 0,
    .Instruction = 0,
    .InstructionMode = QSPI_INSTRUCTION_1_LINE,
    .NbData = 0,
    .SIOOMode = QSPI_SIOO_INST_EVERY_CMD,
};

static const QSPI_CommandTypeDef s_qspi_default_cmd_4_lines = {
    .Address = 0,
    .AddressMode = QSPI_ADDRESS_4_LINES,
    .AddressSize = QSPI_ADDRESS_24_BITS,
    .AlternateByteMode = QSPI_ALTERNATE_BYTES_NONE,
    .AlternateBytes = 0,
    .AlternateBytesSize = 0,
    .DataMode = QSPI_DATA_4_LINES,
    .DdrHoldHalfCycle = 0,
    .DdrMode = QSPI_DDR_MODE_DISABLE,
    .DummyCycles = 0,
    .Instruction = 0,
    .InstructionMode = QSPI_INSTRUCTION_4_LINES,
    .NbData = 0,
    .SIOOMode = QSPI_SIOO_INST_EVERY_CMD,
};

static int qspi_mode = 0; // SPI

static QSPI_CommandTypeDef flash_get_default_cmd()
{
    switch (qspi_mode)
    {
    case 0:
        return s_qspi_default_cmd_1_line;
        break;
    case 1:
        return s_qspi_default_cmd_4_lines;
        break;
    }

    return s_qspi_default_cmd_1_line;
}

static Status flash_wen()
{
    QSPI_CommandTypeDef cmd = flash_get_default_cmd();
    cmd.Instruction = 0x06;
    cmd.NbData = 0;
    cmd.AddressMode = QSPI_ADDRESS_NONE;
    cmd.DataMode = QSPI_DATA_NONE;
    if (HAL_QSPI_Command(&hqspi, &cmd, 100) != HAL_OK)
    {
        return STATUS_ERROR;
    }

    return STATUS_OK;
}

static Status flash_wel()
{
    if (flash_wen() != STATUS_OK)
    {
        return STATUS_ERROR;
    }

    QSPI_CommandTypeDef cmd = flash_get_default_cmd();
    cmd.Instruction = 0x01;
    cmd.NbData = 1;
    cmd.AddressMode = QSPI_ADDRESS_NONE;
    cmd.DataMode = QSPI_DATA_1_LINE;
    uint8_t reg = 0x02;

    if (HAL_QSPI_Command(&hqspi, &cmd, 100) != HAL_OK)
    {
        return STATUS_ERROR;
    }

    if (HAL_QSPI_Transmit(&hqspi, &reg, 100) != HAL_OK)
    {
        return STATUS_ERROR;
    }

    return STATUS_OK;
}

static Status flash_set_qspi_mode()
{
    if (flash_wen() != STATUS_OK)
    {
        return STATUS_ERROR;
    }

    QSPI_CommandTypeDef cmd = flash_get_default_cmd();
    cmd.Instruction = 0x61;
    cmd.NbData = 1;
    cmd.DataMode = QSPI_DATA_1_LINE;
    cmd.AddressMode = QSPI_ADDRESS_NONE;
    uint8_t reg = 0x7F;
    if (HAL_QSPI_Command(&hqspi, &cmd, 100) != HAL_OK)
    {
        return STATUS_ERROR;
    }

    if (HAL_QSPI_Transmit(&hqspi, &reg, 100) != HAL_OK)
    {
        return STATUS_ERROR;
    }

    qspi_mode = 1;

    return STATUS_OK;
}

static Status flash_wait_ready(uint32_t timeout)
{
    QSPI_CommandTypeDef cmd = flash_get_default_cmd();
    cmd.Instruction = 0x05;
    cmd.NbData = 1;
    cmd.AddressMode = QSPI_ADDRESS_NONE;

    uint32_t tickstart = HAL_GetTick();
    uint8_t status = 0x1;
    while (status & 0x1)
    {
        if (HAL_GetTick() - tickstart >= timeout)
        {
            return STATUS_TIMEOUT;
        }

        if (HAL_QSPI_Command(&hqspi, &cmd, 100) != HAL_OK)
        {
            return STATUS_ERROR;
        }

        if (HAL_QSPI_Receive(&hqspi, &status, 100) != HAL_OK)
        {
            return STATUS_ERROR;
        }
    }

    return STATUS_OK;
}

static Status flash_reset()
{
    QSPI_CommandTypeDef cmd = flash_get_default_cmd();
    cmd.Instruction = 0x66; // Reset Enable
    cmd.AddressMode = QSPI_ADDRESS_NONE;
    cmd.DataMode = QSPI_DATA_NONE;

    if (HAL_QSPI_Command(&hqspi, &cmd, 100) != HAL_OK)
    {
        return STATUS_ERROR;
    }

    cmd.Instruction = 0x99; // Reset Memory

    if (HAL_QSPI_Command(&hqspi, &cmd, 100) != HAL_OK)
    {
        return STATUS_ERROR;
    }

    return STATUS_OK;
}

static Status flash_check_id()
{
    QSPI_CommandTypeDef cmd = flash_get_default_cmd();
    cmd.Instruction = 0x9E;
    cmd.NbData = 3;
    cmd.AddressMode = QSPI_ADDRESS_NONE;
    uint8_t id[3];
    if (HAL_QSPI_Command(&hqspi, &cmd, 100) != HAL_OK)
    {
        return STATUS_ERROR;
    }

    if (HAL_QSPI_Receive(&hqspi, id, 100) != HAL_OK)
    {
        return STATUS_ERROR;
    }

    if (id[0] != 0x20 || id[1] != 0xBA || id[2] != 0x18)
    {
        return STATUS_ERROR;
    }

    return STATUS_OK;
}

static QSPI_CommandTypeDef flash_get_mm_read_cmd()
{
    QSPI_CommandTypeDef cmd = flash_get_default_cmd();
    cmd.Instruction = 0xEB;
    cmd.AddressMode = QSPI_ADDRESS_4_LINES;
    cmd.DataMode = QSPI_DATA_4_LINES;
    cmd.DummyCycles = 10;

    return cmd;
}

static Status flash_read(uint32_t addr, uint8_t *buf, int len)
{
    QSPI_CommandTypeDef cmd = flash_get_default_cmd();
    cmd.Instruction = 0xEB;
    cmd.AddressMode = QSPI_ADDRESS_4_LINES;
    cmd.DataMode = QSPI_DATA_4_LINES;
    cmd.DummyCycles = 10;
    cmd.NbData = len;
    cmd.Address = addr;

    if (HAL_QSPI_Command(&hqspi, &cmd, 100) != HAL_OK)
    {
        return STATUS_ERROR;
    }

    if (HAL_QSPI_Receive(&hqspi, buf, 100) != HAL_OK)
    {
        return STATUS_ERROR;
    }

    return STATUS_OK;
}

Status flash_init()
{
    __HAL_RCC_QSPI_CLK_ENABLE();
    __HAL_RCC_QSPI_FORCE_RESET();
    __HAL_RCC_QSPI_RELEASE_RESET();

    GPIO_InitTypeDef GPIO_InitStruct;

    GPIO_InitStruct.Pin = GPIO_PIN_6;
    GPIO_InitStruct.Mode = GPIO_MODE_AF_PP;
    GPIO_InitStruct.Pull = GPIO_NOPULL;
    GPIO_InitStruct.Speed = GPIO_SPEED_FREQ_VERY_HIGH;
    GPIO_InitStruct.Alternate = GPIO_AF10_QSPI;
    HAL_GPIO_Init(GPIOB, &GPIO_InitStruct);

    GPIO_InitStruct.Pin = GPIO_PIN_6 | GPIO_PIN_7 | GPIO_PIN_10;
    GPIO_InitStruct.Mode = GPIO_MODE_AF_PP;
    GPIO_InitStruct.Pull = GPIO_NOPULL;
    GPIO_InitStruct.Speed = GPIO_SPEED_FREQ_VERY_HIGH;
    GPIO_InitStruct.Alternate = GPIO_AF9_QSPI;
    HAL_GPIO_Init(GPIOF, &GPIO_InitStruct);

    GPIO_InitStruct.Pin = GPIO_PIN_8 | GPIO_PIN_9;
    GPIO_InitStruct.Mode = GPIO_MODE_AF_PP;
    GPIO_InitStruct.Pull = GPIO_NOPULL;
    GPIO_InitStruct.Speed = GPIO_SPEED_FREQ_VERY_HIGH;
    GPIO_InitStruct.Alternate = GPIO_AF10_QSPI;
    HAL_GPIO_Init(GPIOF, &GPIO_InitStruct);

    hqspi.Instance = QUADSPI;

    hqspi.Init.ClockPrescaler = 1;
    hqspi.Init.FifoThreshold = 1;
    hqspi.Init.SampleShifting = QSPI_SAMPLE_SHIFTING_HALFCYCLE;
    hqspi.Init.FlashSize = 23;
    hqspi.Init.ChipSelectHighTime = QSPI_CS_HIGH_TIME_5_CYCLE;
    hqspi.Init.ClockMode = QSPI_CLOCK_MODE_0;
    hqspi.Init.FlashID = QSPI_FLASH_ID_1;
    hqspi.Init.DualFlash = QSPI_DUALFLASH_DISABLE;

    if (HAL_QSPI_Init(&hqspi) != HAL_OK)
    {
        return STATUS_ERROR;
    }

    // Reset
    if (flash_reset() != STATUS_OK)
    {
        return STATUS_ERROR;
    }

    // Wait til ready
    flash_wait_ready(100);

    // Write enable latch
    if (flash_wel() != STATUS_OK)
    {
        return STATUS_ERROR;
    }

    // Wait til ready
    flash_wait_ready(100);

    // Verify hardware IDs
    if (flash_check_id() != STATUS_OK)
    {
        return STATUS_ERROR;
    }

    QSPI_MemoryMappedTypeDef cfg;
    cfg.TimeOutActivation = QSPI_TIMEOUT_COUNTER_DISABLE;
    cfg.TimeOutPeriod = 0;

    // Set read command
    QSPI_CommandTypeDef cmd = flash_get_mm_read_cmd();
    HAL_QSPI_MemoryMapped(&hqspi, &cmd, &cfg);

    return STATUS_OK;
}
