griffinross2/Topiary-TrimBot/experimental/cpp/plant_detect/include/still_frame_block.h

#pragma once

#include <block.h>

class StillFrameBlock : public Block {
public:
    StillFrameBlock();
    StillFrameBlock(std::string id);
    void onRender() override;
    void onUpdate() override;

    private:
    cv::Mat m_internalFrame1;
    cv::Mat m_internalFrame2;
};
