griffinross2/Topiary-TrimBot/experimental/cpp/usb_packet_testing/inc/common.h

#pragma once

#include <stdio.h>

// Macro abuse :)
#define TRACE_PRINTF(...)                                \
    do                                                   \
    {                                                    \
        printf("%s:%d: ", __FILE__, __LINE__); \
        printf(__VA_ARGS__);                             \
    } while (0);
