griffinross2/Topiary-TrimBot/experimental/ra8875_test_platformio/src/clocks.cpp

#include "clocks.h"

#include "stm32f0xx_hal.h"
#include "system_stm32f0xx.h"

Status clocks_init() {
    __HAL_RCC_SYSCFG_CLK_ENABLE();
    __HAL_RCC_PWR_CLK_ENABLE();

    __HAL_RCC_GPIOA_CLK_ENABLE();
    __HAL_RCC_GPIOB_CLK_ENABLE();
    __HAL_RCC_GPIOC_CLK_ENABLE();
    __HAL_RCC_GPIOD_CLK_ENABLE();
    __HAL_RCC_GPIOE_CLK_ENABLE();
    __HAL_RCC_GPIOF_CLK_ENABLE();

    return STATUS_OK;
}
