griffinross2/Topiary-TrimBot/experimental/lcd_prototyping_platformio/include/ltdc_dsi.h

#ifndef LTDC_DSI_H
#define LTDC_DSI_H

#include "stm32f4xx_hal.h"

#include "status.h"

#define LTDC_VSYNC 1
#define LTDC_VBP 3
#define LTDC_VFP 1
#define LTDC_HSYNC 1
#define LTDC_HBP 3
#define LTDC_HFP 1
#define LTDC_WIDTH 800
#define LTDC_HEIGHT 480

Status ltdc_dsi_init();
LTDC_HandleTypeDef *ltdc_get_handle();
DSI_HandleTypeDef *dsi_get_handle();

#endif // LTDC_DSI_H
