griffinross2/Topiary-TrimBot/experimental/lcd_prototyping_platformio/include/ft6336g.h

#ifndef FT6336G_H
#define FT6336G_H

#include "status.h"

typedef enum {
    FT6336G_TOUCH_EVENT_DOWN = 0,
    FT6336G_TOUCH_EVENT_UP = 1,
    FT6336G_TOUCH_EVENT_CONTACT = 2,
    FT6336G_TOUCH_EVENT_NONE = 3,
} FT6336G_TouchEvent;

Status ft6336g_init();
void ft6336g_irq();
FT6336G_TouchEvent ft6336g_get_touch_event(int touch_point_index);
Status ft6336g_read_pos(int* x, int* y, int* weight, int touch_point_index);

#define FT6336G_DEV_MODE 0x00
#define FT6336G_GEST_ID 0x01
#define FT6336G_TD_STATUS 0x02
#define FT6336G_P1_XH 0x03
#define FT6336G_P1_XL 0x04
#define FT6336G_P1_YH 0x05
#define FT6336G_P1_YL 0x06
#define FT6336G_P1_WEIGHT 0x07
#define FT6336G_P1_MISC 0x08
#define FT6336G_P2_XH 0x09
#define FT6336G_P2_XL 0x0A
#define FT6336G_P2_YH 0x0B
#define FT6336G_P2_YL 0x0C
#define FT6336G_P2_WEIGHT 0x0D
#define FT6336G_P2_MISC 0x0E
#define FT6336G_TH_GROUP 0x80
#define FT6336G_TH_DIFF 0x85
#define FT6336G_CTRL 0x86
#define FT6336G_TIMEENTERMONITOR 0x87
#define FT6336G_PERIODACTIVE 0x88
#define FT6336G_PERIODMONITOR 0x89
#define FT6336G_RADIAN_VALUE 0x91
#define FT6336G_OFFSET_LEFT_RIGHT 0x92
#define FT6336G_OFFSET_UP_DOWN 0x93
#define FT6336G_DISTANCE_LEFT_RIGHT 0x94
#define FT6336G_DISTANCE_UP_DOWN 0x95
#define FT6336G_DISTANCE_ZOOM 0x96
#define FT6336G_LIB_VER_H 0xA1
#define FT6336G_LIB_VER_L 0xA2
#define FT6336G_CIPHER 0xA3
#define FT6336G_G_MODE 0xA4
#define FT6336G_PWR_MODE 0xA5
#define FT6336G_FIRMID 0xA6
#define FT6336G_FOCALTECH_ID 0xA8
#define FT6336G_RELEASE_CODE_ID 0xAF
#define FT6336G_STATE 0xBC

#endif  // FT6336G_H
